pdsmart/tranZPUter/CPLD/SW/tranZPUterSW.vhd

--------------------------------------------------------------------------------------------------------
--
-- Name:            tranZPUterSW.vhd
-- Created:         June 2020
-- Author(s):       Philip Smart
-- Description:     tranZPUter SW v2.1 - v2.2 CPLD logic definition file.
--                  This module contains the definition of the logic used in v1.0-v1.1 of the tranZPUterSW
--                  project plus enhancements.
--
-- Credits:         
-- Copyright:       (c) 2018-20 Philip Smart <philip.smart@net2net.org>
--
-- History:         June 2020 - Initial creation.
--                  July 2020 - Updated and fixed logic, removed the MZ80B compatibility logic as there
--                              are not enough resources in the CPLD to fully implement.
--                  July 2020 - Changed the keyboard mapping logic to be more compatible. A full swepp 
--                              is made if a read is made to the keyboard data twice in a row as this
--                              signifies a game or program reading BREAK. When the software scans the
--                              keyboard the data is stored into a matrix which is then used for mapping
--                              of the keys.  When the running software accesses the keyboard it reads
--                              from the key matrix and not the PPI. This allows for better compatibility
--                              and a functioning SHIFT+BREAK key. The MZ80A keyboard layout is mapped
--                              as though the keyboard was a real MZ700 keyboard, ie. BREAK key is CLR/HOME
--                              and INST/DEL is CTRL etc. The numeric keypad on the MZ80A is mapped to the
--                              cursor key layout with 7 and 9 acting as INST/DEL. The function keys are
--                              mapped to 1, 0, 00, . and 3 on the numeric keypad.
--                  July 2020 - Making RFS updates I decided that a basic board (ie. no K64F) which would
--                              be used in conjunction with the RFS board needs a secondary clock, 
--                              more especially for the MZ700 3.58MHz mode. I thus added a 50MHz clock 
--                              onto the output that would normally be driven by a K64F. This output
--                              is then divided down to act as the secondary clock. When a mode switch
--                              is made to MZ700 mode the frequency automatically changes.
--                  Mar 2021 -  Better control of the external Asyn BUSRQ/BUSACK was needed, bringing in 
--                              Synchronize with the SW700 development.
--                              the async K64F CTL_BUSRQ into the Z80 clocked domain and adjustment of
--                              mux lines.
--                  Mar 2021 -  Many changes to cater for the MZ-800. The machine has different memory
--                              modes and maps so extensive changes needed.
--                  Apr 2021 -  Removed the v2.1 frequency generator as 2.1 no longer supported. Fixed
--                              issues with adding the MZ-800 using too many resources, made 
--                              compilation conditional.
--
---------------------------------------------------------------------------------------------------------
-- This source file is free software: you can redistribute it and-or modify
-- it under the terms of the GNU General Public License as published
-- by the Free Software Foundation, either version 3 of the License, or
-- (at your option) any later version.
--
-- This source file is distributed in the hope that it will be useful,
-- but WITHOUT ANY WARRANTY; without even the implied warranty of
-- MERCHANTABILITY or FITNESS FOR A PARTICULAR PURPOSE.  See the
-- GNU General Public License for more details.
--
-- You should have received a copy of the GNU General Public License
-- along with this program.  If not, see <http:--www.gnu.org-licenses->.
---------------------------------------------------------------------------------------------------------
library ieee;
library pkgs;
use ieee.std_logic_1164.all;
use ieee.std_logic_unsigned.all;
use ieee.numeric_std.all;
use work.tranZPUterSW_pkg.all;

entity cpld512 is
    --generic (
    --);
    port (    
        -- Z80 Address and Data.
        Z80_HI_ADDR               : inout std_logic_vector(23 downto 16);                -- Hi address. These are the upper bank bits allowing 512K of address space. They are directly set by the K64F when accessing RAM or FPGA and set by the FPGA according to memory mode.
        Z80_RA_ADDR               : out   std_logic_vector(15 downto 12);                -- Row address - RAM is subdivided into 4K blocks which can be remapped as needed. This is required for the MZ80B emulation where memory changes location according to mode.
        Z80_ADDR                  : inout std_logic_vector(15 downto 0);
        Z80_DATA                  : inout std_logic_vector( 7 downto 0);

        -- Z80 Control signals.
        Z80_BUSRQn                : out   std_logic;
        Z80_BUSACKn               : in    std_logic;
        Z80_INTn                  : inout std_logic;
        Z80_IORQn                 : in    std_logic;
        Z80_MREQn                 : inout std_logic;
        Z80_NMIn                  : inout std_logic;
        Z80_RDn                   : in    std_logic;
        Z80_WRn                   : in    std_logic;
        Z80_RESETn                : in    std_logic;                                     -- NB. The CPLD inverts the GCLRn pin, so active negative on the mainboard, active positive inside the CPLD.
        Z80_HALTn                 : in    std_logic;
        Z80_WAITn                 : out   std_logic;
        Z80_M1n                   : in    std_logic;
        Z80_RFSHn                 : in    std_logic;
        Z80_CLK                   : out   std_logic;

        -- K64F control signals.
        CTL_MBSEL                 : in    std_logic;                                     -- Select mainboard, 1 = mainboard, 0 = tranzputer bus.
        CTL_BUSRQn                : in    std_logic;
        CTL_BUSACKn               : out   std_logic;                                     -- Combined BUSACK signal to the K64F
        CTL_HALTn                 : out   std_logic;
        CTL_M1n                   : out   std_logic;
        CTL_RFSHn                 : out   std_logic;
        CTL_WAITn                 : in    std_logic;
        SVCREQn                   : out   std_logic;

        -- Mainboard signals which are blended with K64F signals to activate corresponding Z80 functionality.
        SYS_BUSACKn               : out   std_logic;
        SYS_BUSRQn                : in    std_logic;
        SYS_WAITn                 : in    std_logic;
        SYS_WRn                   : out   std_logic;
        SYS_RDn                   : out   std_logic;    

        -- RAM control.
        RAM_CSn                   : out   std_logic;
        RAM_OEn                   : out   std_logic;
        RAM_WEn                   : out   std_logic;

        -- Graphics Board I/O and Memory Select.
        INCLK                     : in    std_logic;
        OUTDATA                   : out   std_logic_vector(3 downto 0);

        -- Clocks, system and K64F generated.
        SYSCLK                    : in    std_logic;                                     -- Mainboard system clock.
        CTLCLK                    : in    std_logic                                      -- K64F generated secondary CPU clock.
    );
end entity;

architecture rtl of cpld512 is

    -- Definition of a keyboard mapping matrix as an array of registers. The host keyboard is
    -- read into the matrix and the output is mapped according to the target.
    --
    type KeyMatrixType is array(natural range 0 to 9) of std_logic_vector(7 downto 0);

    -- Keyboard mapping signals
    signal KEY_MATRIX             :       KeyMatrixType;
    signal KEY_DATA               :       std_logic_vector(7 downto 0);
    signal KEY_STROBE             :       std_logic_vector(3 downto 0);
    signal KEY_STROBE_LAST        :       std_logic_vector(3 downto 0);
    signal KEY_SUBSTITUTE         :       std_logic;
    signal KEY_SWEEP              :       std_logic;
    signal MB_KEY_STROBE          :       std_logic_vector(3 downto 0);
    signal MB_WRITE_STROBE        :       std_logic;
    signal MB_READ_KEYS           :       std_logic;

    -- CPLD configuration signals.
    signal MODE_CPLD_MZ80K        :       std_logic;
    signal MODE_CPLD_MZ80C        :       std_logic;
    signal MODE_CPLD_MZ1200       :       std_logic;
    signal MODE_CPLD_MZ80A        :       std_logic;
    signal MODE_CPLD_MZ700        :       std_logic;
    signal MODE_CPLD_MZ800        :       std_logic;
    signal MODE_CPLD_MZ80B        :       std_logic;
    signal MODE_CPLD_MZ2000       :       std_logic;
    signal MODE_CPLD_SWITCH       :       std_logic;
    signal MODE_CPLD_MB_VIDEOn    :       std_logic;                                     -- Mainboard video, 0 = enabled, 1 = disabled. 
    signal MODE_HOST_DEFAULT      :       std_logic;                                     -- On cold start, the host acts per original specifications until changed by programming.
    signal CPU_CFG_DATA           :       std_logic_vector(7 downto 0):=(others => '0'); -- CPU Configuration register.
    signal CPLD_CFG_DATA          :       std_logic_vector(7 downto 0):=(others => '0'); -- CPLD Configuration register.
    signal CPLD_INFO_DATA         :       std_logic_vector(7 downto 0);                  -- CPLD status value.
    signal VIDEOMODULE_PRESENT    :       std_logic;                                     -- Automatic flag which is set if the serializer becomes active.

    -- IO Decode signals.
    signal CS_IO_6XXn             :       std_logic;                                     -- IO decode for the 0x60-0x6f region used by the CPLD.
    signal CS_MEM_CFGn            :       std_logic;                                     -- Select for the memory mode latch.
    signal CS_SCK_CTLCLKn         :       std_logic;                                     -- Select for setting the K64F clock as the active Z80 clock.
    signal CS_SCK_SYSCLKn         :       std_logic;                                     -- Select for setting the Mainboard clock as the active Z80 clock.
    signal CS_SCK_RDn             :       std_logic;                                     -- Select to read which clock is active.
    signal CS_CPU_CFGn            :       std_logic;                                     -- Select to set the CPU configuration register.
    signal CS_CPU_INFOn           :       std_logic;                                     -- Select to read the CPU information register.
    signal CS_CPLD_CFGn           :       std_logic;                                     -- Select to set the CPLD configuration register.
    signal CS_CPLD_INFOn          :       std_logic;                                     -- Select to read the CPLD information register.
    signal CS_VIDEOn              :       std_logic;                                     -- Primary select of the FPGA video logic, used to enable control signals in the memory management process.
    signal CS_VIDEO_MEMn          :       std_logic;                                     -- Select to read/write video memory according to mode.
    signal CS_VIDEO_IOn           :       std_logic;                                     -- Select to read/write video IO registers according to mode.
    signal CS_VIDEO_RDn           :       std_logic;                                     -- Select to read video memory and video IO registers according to mode.
    signal CS_VIDEO_WRn           :       std_logic;                                     -- Select to write video memory and video IO registers according to mode.
    signal MEM_MODE_LATCH         :       std_logic_vector(4 downto 0):=(others => '0'); -- Register to store the active memory mode.
    signal MEM_MODE_DATA          :       std_logic_vector(7 downto 0);                  -- Scratch signal to form an 8 bit read of the memory mode register.

    -- SR (LS279) state symbols.
    signal SYSCLK_Q               :       std_logic;
    signal CTLCLK_Q               :       std_logic;
    --
    signal DISABLE_BUSn           :       std_logic;                                     -- Signal to disable access to the mainboard (= 0) via the SYS_BUSACKn signal which tri-states the mainboard logic.
    signal SYS_BUSACKni           :       std_logic := '0';                              -- Signal to hold the current state of the SYS_BUSACKn signal used to activate/tri-state the mainboard logic.

    -- CPU Frequency select logic based on Flip Flops and gates.
    signal SCK_CTLSELn            :       std_logic;
    signal Z80_CLKi               :       std_logic;
    signal CTLCLKi                :       std_logic;
    signal CLK_STATUS_DATA        :       std_logic_vector(7 downto 0);

    -- Video module signals.
    --
    signal VZ80_IORQn             :       std_logic;
    signal OUTBUF                 :       std_logic_vector(3 downto 0);

    -- Video module signal mirrors.
    signal MODE_VIDEO_MZ80A       :       std_logic := '1';                              -- The machine is running in MZ80A mode.
    signal MODE_VIDEO_MZ700       :       std_logic := '0';                              -- The machine is running in MZ700 mode.
    signal MODE_VIDEO_MZ800       :       std_logic := '0';                              -- The machine is running in MZ800 mode.
    signal MODE_VIDEO_MZ80B       :       std_logic := '0';                              -- The machine is running in MZ80B mode.
    signal MODE_VIDEO_MZ80K       :       std_logic := '0';                              -- The machine is running in MZ80K mode.
    signal MODE_VIDEO_MZ80C       :       std_logic := '0';                              -- The machine is running in MZ80C mode.
    signal MODE_VIDEO_MZ1200      :       std_logic := '0';                              -- The machine is running in MZ1200 mode.
    signal MODE_VIDEO_MZ2000      :       std_logic := '0';                              -- The machine is running in MZ2000 mode.
    signal GRAM_PAGE_ENABLE       :       std_logic;                                     -- Graphics mode page enable.
    signal MZ80B_VRAM_HI_ADDR     :       std_logic;                                     -- Video RAM located at D000:FFFF when high.
    signal MZ80B_VRAM_LO_ADDR     :       std_logic;                                     -- Video RAM located at 5000:7FFF when high.
    signal CS_FB_VMn              :       std_logic;                                     -- Chip Select for the Video Mode register.
    signal CS_FB_PAGEn            :       std_logic;                                     -- Chip Select for the Page select register.
    signal CS_IO_CXXn             :       std_logic;                                     -- Chip select for block C0:CF
    signal CS_IO_DXXn             :       std_logic;                                     -- Chip select for block D0:DF
    signal CS_IO_EXXn             :       std_logic;                                     -- Chip select for block E0:EF
    signal CS_IO_FXXn             :       std_logic;                                     -- Chip select for block F0:FF
    signal CS_80B_PIOn            :       std_logic;                                     -- Chip select for MZ80B PIO when in MZ80B mode.

    -- Z80 Wait Insert generator when I/O ports in region > 0XE0 are accessed to give the K64F time to proces them.
  --signal REQ_WAITn            :       std_logic;

    -- Internal control signals.
    signal SYSRESETn              :       std_logic;                                     -- Internal system reset pulse 1 clock period after reset, used to preset registers.
    signal Z80_HI_ADDRi           :       std_logic_vector(23 downto 16);                -- Hi address. These are the upper bank bits allowing 512K of address space. They are directly set by the K64F when accessing RAM or FPGA and set by the FPGA according to memory mode.
    signal Z80_RA_ADDRi           :       std_logic_vector(15 downto 12);                -- Row address - RAM is subdivided into 4K blocks which can be remapped as needed. This is required for the MZ80B emulation where memory changes location according to mode.
    signal CTL_BUSACKni           :       std_logic;                                     -- Buffered BUSACK signal to the K64F to indicate it has control of the bus.
    signal CTL_BUSRQni            :       std_logic;                                     -- Buffered BUSRQ signal. 

    -- RAM select and write signals.
    signal RAM_OEni               :       std_logic;
    signal RAM_CSni               :       std_logic;
    signal RAM_WEni               :       std_logic;

    -- MZ800 Memory map signals.
    signal MAP_0000_0FFF_ROM      :       std_logic;                                     --  
    signal MAP_E000_EFFF_ROM      :       std_logic;                                     --  
    signal MAP_F000_FFFF_ROM      :       std_logic;                                     --  
    signal MAP_1000_1FFF_CGROM    :       std_logic;                                     --  

    signal MAP_0000_0FFF_DRAM     :       std_logic;                                     --  
    signal MAP_1000_1FFF_DRAM     :       std_logic;                                     --  
    signal MAP_2000_2FFF_DRAM     :       std_logic;                                     --  
    signal MAP_3000_3FFF_DRAM     :       std_logic;                                     --  
    signal MAP_4000_4FFF_DRAM     :       std_logic;                                     --  
    signal MAP_5000_5FFF_DRAM     :       std_logic;                                     --  
    signal MAP_6000_6FFF_DRAM     :       std_logic;                                     --  
    signal MAP_7000_7FFF_DRAM     :       std_logic;                                     --  
    signal MAP_8000_8FFF_DRAM     :       std_logic;                                     --  
    signal MAP_9000_9FFF_DRAM     :       std_logic;                                     --  
    signal MAP_A000_AFFF_DRAM     :       std_logic;                                     --  
    signal MAP_B000_BFFF_DRAM     :       std_logic;                                     --  
    signal MAP_C000_CFFF_DRAM     :       std_logic;                                     --  
    signal MAP_D000_DFFF_DRAM     :       std_logic;                                     --  
    signal MAP_E000_EFFF_DRAM     :       std_logic;                                     --  
    signal MAP_F000_FFFF_DRAM     :       std_logic;                                     --  
    signal MAP_8000_8FFF_VRAM     :       std_logic;                                     --  
    signal MAP_9000_9FFF_VRAM     :       std_logic;                                     --  
    signal MAP_A000_AFFF_VRAM     :       std_logic;                                     --  
    signal MAP_B000_BFFF_VRAM     :       std_logic;                                     --  
    signal MAP_C000_CFFF_VRAM     :       std_logic;                                     --  
    signal MAP_D000_DFFF_VRAM     :       std_logic;                                     --  
    signal MAP_E000_E00F_IO       :       std_logic;                                     --  
    signal MAP_INHIBIT            :       std_logic;                                     --  
    signal MAP_TZFS_BANK          :       std_logic;                                     -- Override to use Bank 0 in the 512K Static RAM chup rather than the normal Bank 7. This is so TZFS and MZ-800 IPL are seperate and independent allowing change from one to the other.
    signal MODE_320x200           :       std_logic;                                     -- MZ-800 Set to 320x200 graphics mode.
    signal MODE_640x200           :       std_logic;                                     -- MZ-800 Set to 640x200 graphics mode.

    -- MZ800 IO Signals
    signal CS_GDG_GWF             :       std_logic;                                     -- GDG Write Format Register 
    signal CS_GDG_GRF             :       std_logic;                                     -- GDG Read Format Register 
    signal CS_GDG_CMD             :       std_logic;                                     -- GDG Command Register

    -- Mainboard writeback multiplexing signals.
    signal MB_MREQn               :       std_logic;
    signal MB_BUSRQn              :       std_logic;
    signal MB_ADDR                :       std_logic_vector(15 downto 0);
    signal MB_STATE               :       integer range 0 to 7;
    signal MB_WAITn               :       std_logic;
    signal MB_DELAY_MS            :       unsigned(7 downto 0);

    -- Millisecond timer signals.
    signal DELAY_TICKS            :       unsigned(3 downto 0);
    signal DELAY_US               :       unsigned(9 downto 0);
    signal DELAY_MS_CLK           :       std_logic;

    function to_std_logic(L: boolean) return std_logic is
    begin
        if L then
            return('1');
        else
            return('0');
        end if;
    end function to_std_logic;
begin

    -- Delayed reset process to set defaults on registers as required.
    RESET: process( Z80_CLKi, Z80_RESETn ) begin
        if Z80_RESETn = '0' then
            SYSRESETn          <= '0';
        -- First rising edge the internal system reset is cancelled.
        elsif( rising_edge(Z80_CLKi) ) then
            SYSRESETn          <= '1';
        end if;
    end process;

    -- CPLD/CPU Configuration register.
    --
    -- CPU: (NOT YET IMPLEMENTED IN THE traznZPUter)
    -- Version 1.3-> of the tranZPUter SW-700 provides the ability to instantiate alternative soft CPU's. This register configures the FPGA to enable a soft/hard CPU and the CPLD
    -- is reconfigured to allow a CPU operation on the FPGA side rather than the physical hardware side.
    --
    -- [5:0] - R/W - CPU selection.
    --               000000 = Hard CPU
    --               000001 = T80 CPU
    --               000010 = ZPU Evolution
    --               000100 = Future CPU AAA
    --               001000 = Future CPU AAA
    --               010000 = Future CPU AAA
    --               100000 = Future CPU AAA
    --               All other configurations reserved and default to Hard CPU.
    -- [7]   - R/W - CPU Reset. When active ('1'), hold the CPU in reset, when inactive, commence the reset completion and CPU run.
    --
    -- CPLD:
    -- The mode can be changed by a Z80 transaction write into the register and it is acted upon if the mode switches between differing values. The Z80 write is typically used
    -- by host software such as RFS.
    --
    -- [2:0] - R/W - Mode/emulated machine.
    --               000 = MZ-80K
    --               001 = MZ-80C
    --               010 = MZ-1200
    --               011 = MZ-80A
    --               100 = MZ-700
    --               101 = MZ-800
    --               110 = MZ-80B
    --               111 = MZ-2000
    -- [3]   - R/W - Mainboard Video - 0 = Enable, 1 = Disable - This flag allows Z-80 transactions in the range D000:DFFF to be directed to the mainboard. When disabled all transactions
    --                                 can only be seen by the FPGA video logic. The FPGA uses this flag to enable/disable it's functionality.
    --*[4]   - R/W - Enable WAIT state during frame display period. 1 = Enable, 0 = Disable (default). The flag enables Z80 WAIT assertion during the frame display period. Most video modes
    --                                 use double buffering so this isnt needed, but use of direct writes to the frame buffer in 8 colour mode (ie. 640x200 or 320x200 8 colour) there
    --                                 is not enough memory to double buffer so potentially there could be tear or snow, hence this optional wait generator.
    -- [6:5] - R/W - Mainboard/CPU clock.
    --               000 = Sharp MZ80A 2MHz System Clock.
    --               001 = Sharp MZ80B 4MHz System Clock.
    --               010 = Sharp MZ700 3.54MHz System Clock.
    --               011 -111 = Reserved, defaults to 2MHz System Clock.
    --*[7]   - R/W - Preserve configuration over reset (=1) or set to default on reset (=0).
    -- * = SW700 v1.3 only, not used in other CPLD versions.
    --
    MACHINEMODE: process( Z80_CLKi, Z80_RESETn, SYSRESETn, CS_CPU_CFGn, CS_CPLD_CFGn, CPLD_CFG_DATA, CS_CPLD_INFOn, Z80_DATA )
    begin

        if(Z80_RESETn = '0') then
            MODE_CPLD_SWITCH                  <= '0';
            CPU_CFG_DATA(5 downto 0)          <= (others => '0');
            MAP_TZFS_BANK                     <= '0';
            MODE_640x200                      <= '1';
            MODE_320x200                      <= '0';
         --   MODE_HOST_DEFAULT                 <= '0';
--            if CPLD_CFG_DATA(7) = '0' then
--                -- On MZ-800 hardware, reset the mode to MZ800 as it may be in MZ700 mode prior to reset.
--                if CPLD_HOST_HW = MODE_MZ800 then
--                    CPLD_CFG_DATA             <= "10001101";                            -- Enable Sharp MZ-800 host setting, mainboard video unused, wait state unused.
--                else
--                    -- Default to MZ-80A
--                    CPLD_CFG_DATA             <= "10000011";                            -- Default to Sharp MZ80A
--                end if;
--                MODE_HOST_DEFAULT             <= '1';                                   -- Host runs as original until features enabled.
--            end if;

        elsif SYSRESETn = '0' and CPLD_CFG_DATA(7) = '0' then
            -- On MZ-800 hardware, reset the mode to MZ800 as it may be in MZ700 mode prior to reset.
            if CPLD_HOST_HW = MODE_MZ800 then
                CPLD_CFG_DATA             <= "10001101";                            -- Enable Sharp MZ-800 host setting, mainboard video unused, wait state unused.
            else
                -- Default to MZ-80A
                CPLD_CFG_DATA             <= "10000011";                            -- Default to Sharp MZ80A
            end if;
            MODE_HOST_DEFAULT             <= '1';                                   -- Host runs as original until features enabled.

        elsif(rising_edge(Z80_CLKi)) then

            -- Write to CPU config register.
            if(CS_CPU_CFGn = '0' and Z80_WRn = '0') then

                -- Currently this option is not implemented on the tranZPUter SW so set to default Z80 configuration.
                CPU_CFG_DATA(5 downto 0) <= (others => '0');
            
            -- Write to CPLD config register.
            elsif(CS_CPLD_CFGn = '0' and Z80_WRn = '0') then

                -- Set the mode switch event flag if the mode changes.
                if CPLD_CFG_DATA(2 downto 0) /= Z80_DATA(2 downto 0) then
                    MODE_CPLD_SWITCH          <= '1';
                end if;

                -- On the first mode set, if the mode matches the underlying hardware setup a flag so that all the features are enabled.
                -- This mechanism is to allow a machine to behave as original after a cold power-up if the K64F processor is not running or disabled.
                --
                if CPLD_CFG_DATA(2 downto 0) = std_logic_vector(to_unsigned(CPLD_HOST_HW, 3)) then
                    MODE_HOST_DEFAULT         <= '0';
                end if;

                -- Store the new value into the register, used for read operations.
                CPLD_CFG_DATA                 <= Z80_DATA;
            else
                MODE_CPLD_SWITCH              <= '0';
            end if;

            -- On the MZ800 host capture and action the gate array command as it changes the mode.
            if CPLD_HOST_HW = MODE_MZ800 and CS_GDG_CMD = '0' and Z80_WRn = '0' then

                -- Mode 700 command?
                if Z80_DATA(3 downto 0) = "1000" then
                    CPLD_CFG_DATA(2 downto 0) <= std_logic_vector(to_unsigned(MODE_MZ700, 3));

                -- All zeros then switch mode.
                elsif Z80_DATA(3 downto 0) = "0000" then
                    CPLD_CFG_DATA(2 downto 0) <= std_logic_vector(to_unsigned(MODE_MZ800, 3));

                -- Set 320x200 mode?
                elsif Z80_DATA(3 downto 2) = "00" then
                    MODE_640x200              <= '0';
                    MODE_320x200              <= '1';

                -- Set 640x200 mode?
                elsif Z80_DATA(3 downto 2) = "01" then
                    MODE_640x200              <= '1';
                    MODE_320x200              <= '0';
                end if;

                -- A non-standard GDG Command, if bit 7 is set swap ROM banks to allow TZFS to run.
                if Z80_DATA(7) = '1' then
                    MAP_TZFS_BANK             <= '1';
                end if;
            end if;
        end if;
    end process;

    -- MZ-80A/MZ-700 target hardware, generate the original memory management mode logic.
    --
    MEMORYMODE80A: if CPLD_HOST_HW = MODE_MZ80A or CPLD_HOST_HW = MODE_MZ700 generate

        MEMORYMODE: process( Z80_CLKi, Z80_RESETn, SYSRESETn, CS_MEM_CFGn, Z80_IORQn, Z80_WRn, Z80_ADDR, Z80_DATA, CPLD_CFG_DATA, MODE_640x200 )
            variable mz700_LOWER_RAM      : std_logic;
            variable mz700_UPPER_RAM      : std_logic;
            variable mz700_INHIBIT        : std_logic;
            variable MODE_CPLD_LAST       : std_logic_vector(2 downto 0);
        begin

            if(Z80_RESETn = '0') then
                mz700_LOWER_RAM           := '0';
                mz700_UPPER_RAM           := '0';
                mz700_INHIBIT             := '0';
                MODE_CPLD_LAST            := std_logic_vector(to_unsigned(CPLD_HOST_HW, MODE_CPLD_LAST'length));

            -- On power up reset, default to original configuration.
            elsif SYSRESETn = '0' and CPLD_CFG_DATA(7) = '0' then
                -- Default to MZ-700/MZ-80A
                MEM_MODE_LATCH            <= std_logic_vector(to_unsigned(TZMM_ORIG, MEM_MODE_LATCH'length));

            -- A direct write to the memory latch stores the required memory mode into the latch.
            elsif (CS_MEM_CFGn = '0' and Z80_WRn = '0') then
                MEM_MODE_LATCH            <= Z80_DATA(4 downto 0);

            elsif(Z80_CLKi'event and Z80_CLKi = '1') then

                -- Each clock remember the current mode to detect a change.
                MODE_CPLD_LAST            := CPLD_CFG_DATA(2 downto 0);

                -- Check for MZ700 Mode memory changes and adjust current memory mode setting.
                --
                if(MODE_CPLD_MZ700 = '1' and Z80_IORQn = '0' and Z80_M1n = '1' and Z80_ADDR(7 downto 3) = "11100") then

                    -- MZ700 memory mode switch?
                    --         0x0000:0x0FFF     0xD000:0xFFFF
                    -- 0xE0 =  DRAM
                    -- 0xE1 =                    DRAM
                    -- 0xE2 =  MONITOR
                    -- 0xE3 =                    Memory Mapped I/O
                    -- 0xE4 =  MONITOR           Memory Mapped I/O
                    -- 0xE5 =                    Inhibit
                    -- 0xE6 =                    Return to state prior to 0xE5
                    case Z80_ADDR(2 downto 0) is
                        -- 0xE0
                        when "000" =>
                            mz700_LOWER_RAM            := '1';

                        -- 0xE1
                        when "001" =>
                            mz700_UPPER_RAM            := '1';

                        -- 0xE2
                        when "010" =>
                            mz700_LOWER_RAM            := '0';

                        -- 0xE3
                        when "011" =>
                            mz700_UPPER_RAM            := '0';

                        -- 0xE4
                        when "100" =>
                            mz700_LOWER_RAM            := '0';
                            mz700_UPPER_RAM            := '0';

                        -- 0xE5
                        when "101" =>
                            mz700_INHIBIT              := '1';

                        -- 0xE6
                        when "110" =>
                            mz700_INHIBIT              := '0';

                        -- 0xE7
                        when "111" =>
                    end case;

                    if(mz700_INHIBIT = '0' and mz700_LOWER_RAM = '0' and mz700_UPPER_RAM = '0') then
                        MEM_MODE_LATCH(4 downto 0)     <= std_logic_vector(to_unsigned(TZMM_TZFS,    MEM_MODE_LATCH'length));

                    elsif(mz700_INHIBIT = '0' and mz700_LOWER_RAM = '1' and mz700_UPPER_RAM = '0') then
                        MEM_MODE_LATCH(4 downto 0)     <= std_logic_vector(to_unsigned(TZMM_MZ700_0, MEM_MODE_LATCH'length));

                    elsif(mz700_INHIBIT = '0' and mz700_LOWER_RAM = '0' and mz700_UPPER_RAM = '1') then
                        MEM_MODE_LATCH(4 downto 0)     <= std_logic_vector(to_unsigned(TZMM_MZ700_1, MEM_MODE_LATCH'length));

                    elsif(mz700_INHIBIT = '0' and mz700_LOWER_RAM = '1' and mz700_UPPER_RAM = '1') then
                        MEM_MODE_LATCH(4 downto 0)     <= std_logic_vector(to_unsigned(TZMM_MZ700_2, MEM_MODE_LATCH'length));

                    elsif(mz700_INHIBIT = '1' and mz700_LOWER_RAM = '0') then
                        MEM_MODE_LATCH(4 downto 0)     <= std_logic_vector(to_unsigned(TZMM_MZ700_3, MEM_MODE_LATCH'length));

                    elsif(mz700_INHIBIT = '1' and mz700_LOWER_RAM = '1') then
                        MEM_MODE_LATCH(4 downto 0)     <= std_logic_vector(to_unsigned(TZMM_MZ700_4, MEM_MODE_LATCH'length));
                    else
                        null;
                    end if;

                -- Unknown event!
                else
                    null;
                end if;
            end if;
        end process;
    end generate;

    -- MZ-800 target hardware, generate the newer memory management mode logic.
    --
    MEMORYMODE800: if CPLD_HOST_HW = MODE_MZ800 generate

        -- Memory mode latch. This latch stores the current memory mode (or Bank Paging Scheme) according to the running software.
        --
        MEMORYMODE: process( Z80_CLKi, Z80_RESETn, SYSRESETn, CS_MEM_CFGn, Z80_IORQn, Z80_WRn, Z80_ADDR, Z80_DATA, CPLD_CFG_DATA, MODE_640x200 )
            variable mz700_LOWER_RAM      : std_logic;
            variable mz700_UPPER_RAM      : std_logic;
            variable mz700_INHIBIT        : std_logic;
            variable MODE_CPLD_LAST       : std_logic_vector(2 downto 0);
        begin

            if(Z80_RESETn = '0') then
    --            -- On power up reset, default to original configuration.
    --            if CPLD_CFG_DATA(7) = '0' then
    --                -- Default to MZ-700/MZ-80A
    --                MEM_MODE_LATCH        <= std_logic_vector(to_unsigned(TZMM_ORIG, MEM_MODE_LATCH'length));
    --
    --            -- MZ-800 mode
    --            --elsif CPLD_HOST_HW = MODE_MZ800 then
    --            --    MEM_MODE_LATCH        <= std_logic_vector(to_unsigned(TZMM_MZ800, MEM_MODE_LATCH'length));
    --            end if;
                mz700_LOWER_RAM           := '0';
                mz700_UPPER_RAM           := '0';
                mz700_INHIBIT             := '0';

                -- Setup MZ-800 control on reset to MZ-800 startup memory map.
                MAP_0000_0FFF_ROM         <= '1';
                MAP_1000_1FFF_CGROM       <= '1';
                MAP_2000_2FFF_DRAM        <= '1';
                MAP_3000_3FFF_DRAM        <= '1';
                MAP_4000_4FFF_DRAM        <= '1';
                MAP_5000_5FFF_DRAM        <= '1';
                MAP_6000_6FFF_DRAM        <= '1';
                MAP_7000_7FFF_DRAM        <= '1';
                MAP_A000_AFFF_DRAM        <= not MODE_640x200;
                MAP_B000_BFFF_DRAM        <= not MODE_640x200;
                MAP_C000_CFFF_DRAM        <= '1';
                MAP_D000_DFFF_DRAM        <= '1';
                MAP_8000_8FFF_VRAM        <= '1';
                MAP_9000_9FFF_VRAM        <= '1';
                MAP_A000_AFFF_VRAM        <= MODE_640x200;
                MAP_B000_BFFF_VRAM        <= MODE_640x200;
                MAP_E000_EFFF_ROM         <= '1';
                MAP_F000_FFFF_ROM         <= '1';
                -- Clear remaining flags.
                MAP_0000_0FFF_DRAM        <= '0';
                MAP_1000_1FFF_DRAM        <= '0';
                MAP_8000_8FFF_DRAM        <= '0';
                MAP_9000_9FFF_DRAM        <= '0';
                MAP_E000_EFFF_DRAM        <= '0';
                MAP_F000_FFFF_DRAM        <= '0';
                MAP_C000_CFFF_VRAM        <= '0';
                MAP_D000_DFFF_VRAM        <= '0';
                MAP_E000_E00F_IO          <= '0';
                MAP_INHIBIT               <= '0';

                MODE_CPLD_LAST            := std_logic_vector(to_unsigned(CPLD_HOST_HW, MODE_CPLD_LAST'length));

            -- On power up reset, default to original configuration.
            elsif SYSRESETn = '0' and CPLD_CFG_DATA(7) = '0' then
                -- Default to MZ-700/MZ-80A
                MEM_MODE_LATCH            <= std_logic_vector(to_unsigned(TZMM_ORIG, MEM_MODE_LATCH'length));

                -- MZ-800 mode
                --elsif CPLD_HOST_HW = MODE_MZ800 then
                --    MEM_MODE_LATCH        <= std_logic_vector(to_unsigned(TZMM_MZ800, MEM_MODE_LATCH'length));
     

            -- A direct write to the memory latch stores the required memory mode into the latch.
            elsif (CS_MEM_CFGn = '0' and Z80_WRn = '0') then
                MEM_MODE_LATCH            <= Z80_DATA(4 downto 0);

            elsif(Z80_CLKi'event and Z80_CLKi = '1') then

                -- Cater for mode switches made by software between the MZ800 and MZ700 modes.
                --.
    --            if MODE_CPLD_LAST = MODE_MZ700 and MODE_CPLD_MZ800 = '1' then
    --                MAP_0000_0FFF_ROM     <= '1';
    --                MAP_1000_1FFF_CGROM   <= '1';
    --                MAP_2000_2FFF_DRAM    <= '1';
    --                MAP_3000_3FFF_DRAM    <= '1';
    --                MAP_4000_4FFF_DRAM    <= '1';
    --                MAP_5000_5FFF_DRAM    <= '1';
    --                MAP_6000_6FFF_DRAM    <= '1';
    --                MAP_7000_7FFF_DRAM    <= '1';
    --                MAP_A000_AFFF_DRAM    <= not MODE_640x200;
    --                MAP_B000_BFFF_DRAM    <= not MODE_640x200;
    --                MAP_C000_CFFF_DRAM    <= '1';
    --                MAP_D000_DFFF_DRAM    <= '1';
    --                MAP_8000_8FFF_VRAM    <= '1';
    --                MAP_9000_9FFF_VRAM    <= '1';
    --                MAP_A000_AFFF_VRAM    <= MODE_640x200;
    --                MAP_B000_BFFF_VRAM    <= MODE_640x200;
    --                MAP_E000_EFFF_ROM     <= '1';
    --                MAP_F000_FFFF_ROM     <= '1';
    --                -- Clear remaining flags.
    --                MAP_0000_0FFF_DRAM    <= '0';
    --                MAP_1000_1FFF_DRAM    <= '0';
    --                MAP_8000_8FFF_DRAM    <= '0';
    --                MAP_9000_9FFF_DRAM    <= '0';
    --                MAP_E000_EFFF_DRAM    <= '0';
    --                MAP_F000_FFFF_DRAM    <= '0';
    --                MAP_C000_CFFF_VRAM    <= '0';
    --                MAP_D000_DFFF_VRAM    <= '0';
    --                MAP_E000_E00F_IO      <= '0';
    --                MAP_INHIBIT           <= '0';
    --
    --            elsif MODE_CPLD_LAST = MODE_MZ800 and MODE_CPLD_MZ700 = '1' then
    --                MAP_0000_0FFF_ROM     <= '1';
    --                MAP_1000_1FFF_DRAM    <= '1';
    --                MAP_2000_2FFF_DRAM    <= '1';
    --                MAP_3000_3FFF_DRAM    <= '1';
    --                MAP_4000_4FFF_DRAM    <= '1';
    --                MAP_5000_5FFF_DRAM    <= '1';
    --                MAP_6000_6FFF_DRAM    <= '1';
    --                MAP_7000_7FFF_DRAM    <= '1';
    --                MAP_8000_8FFF_DRAM    <= '1';
    --                MAP_9000_9FFF_DRAM    <= '1';
    --                MAP_A000_AFFF_DRAM    <= '1';
    --                MAP_B000_BFFF_DRAM    <= '1';
    --                MAP_C000_CFFF_DRAM    <= '1';
    --                MAP_D000_DFFF_VRAM    <= '1';
    --                MAP_E000_E00F_IO      <= '1';
    --                MAP_E000_EFFF_ROM     <= '1';
    --                MAP_F000_FFFF_ROM     <= '1';
    --                -- Clear remaining flags.
    --                MAP_1000_1FFF_CGROM   <= '0';
    --                MAP_0000_0FFF_DRAM    <= '0';
    --                MAP_D000_DFFF_DRAM    <= '0';
    --                MAP_E000_EFFF_DRAM    <= '0';
    --                MAP_F000_FFFF_DRAM    <= '0';
    --                MAP_8000_8FFF_VRAM    <= '0';
    --                MAP_9000_9FFF_VRAM    <= '0';
    --                MAP_A000_AFFF_VRAM    <= '0';
    --                MAP_B000_BFFF_VRAM    <= '0';
    --                MAP_C000_CFFF_VRAM    <= '0';
    --                MAP_INHIBIT           <= '0';
    --
    --            end if;

                -- Each clock remember the current mode to detect a change.
                MODE_CPLD_LAST            := CPLD_CFG_DATA(2 downto 0);

                -- MZ700/MZ800 memory mode switch?
                --
                --             MZ-700                                                     MZ-800
                --            |0000:0FFF|1000:1FFF|1000:CFFF|C000:CFFF|D000:FFFF          |0000:7FFF|1000:1FFF|2000:7FFF|8000:BFFF|C000:CFFF|C000:DFFF|E000:FFFF
                --            --------------------------------------------------          ----------------------------------------------------------------------
                -- OUT 0xE0 = |DRAM     |         |         |         |                   |DRAM     |         |         |         |         |         |            
                -- OUT 0xE1 = |         |         |         |         |DRAM               |         |         |         |         |         |         |DRAM
                -- OUT 0xE2 = |MONITOR  |         |         |         |                   |MONITOR  |         |         |         |         |         |             
                -- OUT 0xE3 = |         |         |         |         |Memory Mapped I/O  |         |         |         |         |         |         |Upper MONITOR ROM             
                -- OUT 0xE4 = |MONITOR  |         |DRAM     |         |Memory Mapped I/O  |MONITOR  |CGROM    |DRAM     |VRAM     |         |DRAM     |Upper MONITOR ROM
                -- OUT 0xE5 = |         |         |         |         |Inhibit            |         |         |         |         |         |         |Inhibit
                -- OUT 0xE6 = |         |         |         |         |<return>           |         |         |         |         |         |         |<return>
                -- IN  0xE0 = |         |CGROM*   |         |VRAM*    |                   |         |CGROM    |         |VRAM     |         |         |              
                -- IN  0xE1 = |         |DRAM     |         |DRAM     |                   |         |<return> |         |DRAM     |         |         |                                                                           
                --
                -- <return> = Return to the state prior to the complimentary command being invoked.
                -- * = MZ-800 host only.

                -- On MZ-800 hardware the MZ-700 mode is not quite the same so I've elected to use seperate decoding. You thus have MZ700/MZ800 modes on MZ800 hardware and MZ700 modes on 
                -- MZ700/MZ-80A hardware.
                --
                if((MODE_CPLD_MZ700 = '1' or MODE_CPLD_MZ800 = '1') and Z80_IORQn = '0' and Z80_M1n = '1' and Z80_ADDR(7 downto 3) = "11100") then

                    case Z80_ADDR(2 downto 0) is
                        -- 0xE0
                        when "000" =>
                            -- To cater for the CGROM being paged into the address space we use an override rather than a seperate memory mode.
                            if Z80_RDn = '0' then
                                MAP_1000_1FFF_DRAM     <= '0';
                                MAP_1000_1FFF_CGROM    <= '1';
                                if MODE_CPLD_MZ800 = '1' then
                                    MAP_8000_8FFF_VRAM <= '1';
                                    MAP_9000_9FFF_VRAM <= '1';
                                    MAP_A000_AFFF_VRAM <= MODE_640x200;
                                    MAP_B000_BFFF_VRAM <= MODE_640x200;
                                    MAP_8000_8FFF_DRAM <= '0';
                                    MAP_9000_9FFF_DRAM <= '0';
                                    MAP_A000_AFFF_DRAM <= not MODE_640x200;
                                    MAP_B000_BFFF_DRAM <= not MODE_640x200;
                                else
                                    MAP_C000_CFFF_VRAM <= '1';
                                    MAP_C000_CFFF_DRAM <= '0';
                                end if;

                            elsif MODE_CPLD_MZ800 = '1' then
                                MAP_0000_0FFF_DRAM     <= '1';
                                MAP_1000_1FFF_DRAM     <= '1';
                                MAP_2000_2FFF_DRAM     <= '1';
                                MAP_3000_3FFF_DRAM     <= '1';
                                MAP_4000_4FFF_DRAM     <= '1';
                                MAP_5000_5FFF_DRAM     <= '1';
                                MAP_6000_6FFF_DRAM     <= '1';
                                MAP_7000_7FFF_DRAM     <= '1';
                                MAP_0000_0FFF_ROM      <= '0';
                                MAP_1000_1FFF_CGROM    <= '0';
                            else
                                MAP_0000_0FFF_DRAM     <= '1';
                                MAP_1000_1FFF_DRAM     <= '1';
                                MAP_2000_2FFF_DRAM     <= '1';
                                MAP_3000_3FFF_DRAM     <= '1';
                                MAP_4000_4FFF_DRAM     <= '1';
                                MAP_5000_5FFF_DRAM     <= '1';
                                MAP_6000_6FFF_DRAM     <= '1';
                                MAP_7000_7FFF_DRAM     <= '1';
                                MAP_8000_8FFF_DRAM     <= '1';
                                MAP_9000_9FFF_DRAM     <= '1';
                                MAP_A000_AFFF_DRAM     <= '1';
                                MAP_B000_BFFF_DRAM     <= '1';
                                MAP_C000_CFFF_DRAM     <= '1';
                                MAP_0000_0FFF_ROM      <= '0';
                                MAP_1000_1FFF_CGROM    <= '0';
                            end if;

                        -- 0xE1
                        when "001" =>
                            if Z80_RDn = '0' then
                                MAP_1000_1FFF_DRAM     <= '1';
                                MAP_1000_1FFF_CGROM    <= '0';

                                if MODE_CPLD_MZ800 = '1' then
                                    MAP_8000_8FFF_DRAM <= '1';
                                    MAP_9000_9FFF_DRAM <= '1';
                                    MAP_A000_AFFF_DRAM <= '1';
                                    MAP_B000_BFFF_DRAM <= '1';
                                    MAP_8000_8FFF_VRAM <= '0';
                                    MAP_9000_9FFF_VRAM <= '0';
                                    MAP_A000_AFFF_VRAM <= '0';
                                    MAP_B000_BFFF_VRAM <= '0';
                                else
                                    MAP_C000_CFFF_DRAM <= '1';
                                    MAP_C000_CFFF_VRAM <= '0';
                                end if;

                            elsif MODE_CPLD_MZ800 = '1' then
                                MAP_E000_EFFF_DRAM     <= '1';
                                MAP_F000_FFFF_DRAM     <= '1';
                                MAP_E000_EFFF_ROM      <= '0';
                                MAP_F000_FFFF_ROM      <= '0';
                                MAP_E000_E00F_IO       <= '0';
                            else
                                MAP_D000_DFFF_DRAM     <= '1';
                                MAP_E000_EFFF_DRAM     <= '1';
                                MAP_F000_FFFF_DRAM     <= '1';
                                MAP_D000_DFFF_VRAM     <= '0';
                                MAP_E000_EFFF_ROM      <= '0';
                                MAP_F000_FFFF_ROM      <= '0';
                                MAP_E000_E00F_IO       <= '0';
                            end if;

                        -- 0xE2
                        when "010" =>
                            MAP_0000_0FFF_ROM          <= '1';
                            MAP_0000_0FFF_DRAM         <= '0';

                        -- 0xE3
                        when "011" =>
                            if MODE_CPLD_MZ800 = '1' then
                                MAP_E000_EFFF_ROM      <= '1';
                                MAP_F000_FFFF_ROM      <= '1';
                                MAP_E000_E00F_IO       <= '0';
                                MAP_E000_EFFF_DRAM     <= '0';
                                MAP_F000_FFFF_DRAM     <= '0';
                            else
                                MAP_D000_DFFF_VRAM     <= '1';
                                MAP_E000_E00F_IO       <= '1';
                                MAP_E000_EFFF_ROM      <= '1';
                                MAP_F000_FFFF_ROM      <= '1';
                            end if;

                        -- 0xE4
                        when "100" =>
                            if MODE_CPLD_MZ800 = '1' then
                                MAP_0000_0FFF_ROM      <= '1';
                                MAP_1000_1FFF_CGROM    <= '1';
                                MAP_2000_2FFF_DRAM     <= '1';
                                MAP_3000_3FFF_DRAM     <= '1';
                                MAP_4000_4FFF_DRAM     <= '1';
                                MAP_5000_5FFF_DRAM     <= '1';
                                MAP_6000_6FFF_DRAM     <= '1';
                                MAP_7000_7FFF_DRAM     <= '1';
                                MAP_A000_AFFF_DRAM     <= not MODE_640x200;
                                MAP_B000_BFFF_DRAM     <= not MODE_640x200;
                                MAP_C000_CFFF_DRAM     <= '1';
                                MAP_D000_DFFF_DRAM     <= '1';
                                MAP_8000_8FFF_VRAM     <= '1';
                                MAP_9000_9FFF_VRAM     <= '1';
                                MAP_A000_AFFF_VRAM     <= MODE_640x200;
                                MAP_B000_BFFF_VRAM     <= MODE_640x200;
                                MAP_E000_EFFF_ROM      <= '1';
                                MAP_F000_FFFF_ROM      <= '1';
                                -- Clear remaining flags.
                                MAP_0000_0FFF_DRAM     <= '0';
                                MAP_1000_1FFF_DRAM     <= '0';
                                MAP_8000_8FFF_DRAM     <= '0';
                                MAP_9000_9FFF_DRAM     <= '0';
                                MAP_E000_EFFF_DRAM     <= '0';
                                MAP_F000_FFFF_DRAM     <= '0';
                                MAP_C000_CFFF_VRAM     <= '0';
                                MAP_D000_DFFF_VRAM     <= '0';
                                MAP_E000_E00F_IO       <= '0';
                                MAP_INHIBIT            <= '0';

                            else
                                MAP_0000_0FFF_ROM      <= '1';
                                MAP_1000_1FFF_DRAM     <= '1';
                                MAP_2000_2FFF_DRAM     <= '1';
                                MAP_3000_3FFF_DRAM     <= '1';
                                MAP_4000_4FFF_DRAM     <= '1';
                                MAP_5000_5FFF_DRAM     <= '1';
                                MAP_6000_6FFF_DRAM     <= '1';
                                MAP_7000_7FFF_DRAM     <= '1';
                                MAP_8000_8FFF_DRAM     <= '1';
                                MAP_9000_9FFF_DRAM     <= '1';
                                MAP_A000_AFFF_DRAM     <= '1';
                                MAP_B000_BFFF_DRAM     <= '1';
                                MAP_C000_CFFF_DRAM     <= '1';
                                MAP_D000_DFFF_VRAM     <= '1';
                                MAP_E000_E00F_IO       <= '1';
                                MAP_E000_EFFF_ROM      <= '1';
                                MAP_F000_FFFF_ROM      <= '1';
                                -- Clear remaining flags.
                                MAP_0000_0FFF_DRAM     <= '0';
                                MAP_1000_1FFF_CGROM    <= '0';
                                MAP_D000_DFFF_DRAM     <= '0';
                                MAP_E000_EFFF_DRAM     <= '0';
                                MAP_F000_FFFF_DRAM     <= '0';
                                MAP_8000_8FFF_VRAM     <= '0';
                                MAP_9000_9FFF_VRAM     <= '0';
                                MAP_A000_AFFF_VRAM     <= '0';
                                MAP_B000_BFFF_VRAM     <= '0';
                                MAP_C000_CFFF_VRAM     <= '0';
                                MAP_INHIBIT            <= '0';
                            end if;

                        -- 0xE5
                        when "101" =>
                            MAP_INHIBIT                <= '1';

                        -- 0xE6
                        when "110" =>
                            MAP_INHIBIT                <= '0';

                        -- 0xE7
                        when "111" =>
                    end case;

                    -- Single memory map mode to handle the MZ-800, decoding is done in the memory management process.
                    if MODE_HOST_DEFAULT = '0' then
                        MEM_MODE_LATCH(4 downto 0)     <= std_logic_vector(to_unsigned(TZMM_MZ800, MEM_MODE_LATCH'length));
                    end if;

                -- Unknown event!
                else
                    null;
                end if;
            end if;
        end process;
    end generate;

    -- Process to map host keyboard to realise compatibility with other Sharp machines.
    -- Currently the host can be a Sharp MZ-80A or MZ-800. Target (emulated) machines will be mapped accordingly.
    -- will appear as the target keyboard.
    USEKEYMAPPER: if CPLD_HOST_HW = MODE_MZ80A generate

        KEYMAPPER: process( Z80_CLKi, Z80_RESETn, CS_MEM_CFGn, Z80_IORQn, Z80_ADDR, Z80_DATA )
            variable DELAY_MS_CLK_LAST  : std_logic;
        begin

            if Z80_RESETn = '0' then
                KEY_SUBSTITUTE          <= '0';
                KEY_SWEEP               <= '0';
                MB_STATE                <= 0;
                MB_BUSRQn               <= '1';
                MB_MREQn                <= '1';
                MB_WRITE_STROBE         <= '0';
                MB_READ_KEYS            <= '0';
                MB_WAITn                <= '1';
                MB_ADDR                 <= (others => '0');
                MB_DELAY_MS             <= (others => '0');
                MB_KEY_STROBE           <= (others => '0');
                KEY_STROBE              <= (others => '0');
                KEY_STROBE_LAST         <= (others => '0');

            elsif Z80_CLKi'event and Z80_CLKi = '1' then

                -- Millisecond down counter.
                if DELAY_MS_CLK = '1' and DELAY_MS_CLK_LAST = '0' then
                    if MB_DELAY_MS /= 0 then
                        MB_DELAY_MS     <= MB_DELAY_MS - 1;
                    end if;
                end if;
                DELAY_MS_CLK_LAST       := DELAY_MS_CLK;

                -- When inactive, wait for a Z80 I/O transaction that needs writeback.
                --
                if MODE_CPLD_MZ700 = '1' then

                    -- Auto scanning state machine. When the MZ700 isnt scanning the keys this FSM scans them to be ready
                    -- to respond to events such as BREAK key detection. Normally the FSM wont run as the MZ700 scans the keys in
                    -- software but when the MZ700 runs some kinds of software the scans stop and occasionally the BREAK/SHIFT line 9 is scanned.
                    -- Under these circumstances the FSM will make a full sweep of the keys.
                    --
                    -- Configurable delay, a tick by tick timer and a millisecond timer, halts all actions whilst the timer > 0.
                    if MB_DELAY_MS /= 0 then

                    -- If the Z80 Bus has not been requested and we need to make a key sweep, request the bus and start the sweep.
                    elsif Z80_MREQn = '1' and MB_BUSRQn = '1' and MB_WAITn = '1' and KEY_SWEEP = '1' and KEY_SUBSTITUTE = '0' then
                        MB_BUSRQn       <= '0';

                    -- When the Z80 bus is available, run the FSM.
                    elsif MB_BUSRQn = '0' and Z80_BUSACKn = '0' then

                        -- Move along the state machine, next state can be overriden if required.
                        --
                        if MB_STATE = 6 then
                            MB_STATE                <= 0;
                        else
                            MB_STATE                <= MB_STATE+1;
                        end if;

                        -- FSM.
                        case MB_STATE is
                            -- Setup to write the strobe value to PPI A.
                            when 0 =>
                                MB_ADDR             <= X"E000";
                                KEY_DATA            <= "1111" & MB_KEY_STROBE;
        
                            -- Allow at least 1 cycles for the MREQ signal to settle.
                            when 1 =>
                                MB_MREQn            <= '0';

                            -- Allow at least 1 cycle for the write pulse.
                            when 2 =>
                                MB_WRITE_STROBE     <= '1';
        
                            -- Terminate write pulse.
                            when 3 =>
                                MB_MREQn            <= '1';
                                MB_WRITE_STROBE     <= '0';
        
                            -- Setup for a read of the key data from PPI B.
                            when 4 =>
                                MB_ADDR             <= X"E001";
        
                            -- Allow at least 2 cycles for the data to become available.
                            when 5 =>
                                MB_MREQn            <= '0';
                                MB_READ_KEYS        <= '1';
        
                            -- Read the key data into the matrix for later mapping.
                            when 6 =>
                                KEY_MATRIX(to_integer(unsigned(MB_KEY_STROBE))) <= Z80_DATA;
                                MB_MREQn            <= '1';
                                MB_READ_KEYS        <= '0';
        
                                if unsigned(MB_KEY_STROBE) = 9 then
                                    MB_KEY_STROBE   <= (others => '0');
                                    MB_DELAY_MS     <= X"FA";                     -- 250ms delay between key sweeps with a 3.58MHz clock to prevent excessive scanning.
                                    KEY_SWEEP       <= '0';
                                    MB_BUSRQn       <= '1';
                                else
                                    MB_KEY_STROBE   <= MB_KEY_STROBE + 1;
                                    MB_BUSRQn       <= '1';
                                end if;
        
                            when others =>
                                MB_STATE            <= 0;
                        end case;
                    end if;

                    -- When the Z80 isnt tri-stated process the memory operations and act on required triggers.
                    --
                    if MB_BUSRQn = '1' and Z80_BUSACKn = '1' then
                        -- Detect a strobe output write and store it - this is used as the index into the key matrix for each read operation.
                        if(Z80_MREQn = '0' and Z80_ADDR(15 downto 0) = X"E000" and Z80_DATA(7) = '1') then
                            KEY_STROBE              <= Z80_DATA(3 downto 0);
                        end if;

                        -- On a keyscan read data into the matrix and raise the substitue flag. This flag will disable the mainboard (tri-state it) so that the data lines are not driven. The mapped
                        -- data is then output on the data bus by the CPLD which the Z80 reads.
                        if(Z80_MREQn = '0' and Z80_ADDR(15 downto 0) = X"E001") then

                            -- If this is the first loop, set a 1 cycle wait to allow us to read in the scanned data before overriding with the mapped data. The Z80 cycle is short so without the wait
                            -- we cant reliably read the data being output from the 8255.
                            if MB_WAITn = '1' and KEY_SUBSTITUTE = '0' then
                                MB_WAITn            <= '0';
                                MB_BUSRQn           <= '1'; 
                            else
                                -- 2nd cycle we release the WAIT state and override the data being output by the 8255 with the mapped equivalent.
                                MB_WAITn            <= '1';
                                KEY_SUBSTITUTE      <= '1';

                                -- On the 2nd loop the data from the 8255 key scan has settled on the bus so can be captured.
                                if KEY_SUBSTITUTE = '0' then
                                    KEY_MATRIX(to_integer(unsigned(KEY_STROBE))) <= Z80_DATA;
                                end if;

                                -- Remember last key strobe as we need to detect a scan to the same row more than once, this is typically used for BREAK detection or single key detection.
                                -- In these cases we make an automated sweep of the entire keyboard as keys on the host are spread out on different strobe lines whereas the machine we are mapping to
                                -- has them on one strobe line.
                                KEY_STROBE_LAST     <= KEY_STROBE;
                                if KEY_STROBE_LAST = KEY_STROBE and KEY_SWEEP = '0' then
                                    KEY_SWEEP       <= '1';
                                end if;
                            end if;

                            -- Actual keyboard mapping. The Sharp MZ-80A key codes are scanned into a 10x8 matrix and then this matrix is indexed to extract the keycodes for the machine we
                            -- are being compatible with.
                            --
                            -- MZ-80A Keyboard -> MZ-700 mapping.
                            if MODE_CPLD_MZ700 = '1' then
                                case KEY_STROBE is
                                    --                     D7                D6                D5                D4                D3                D2                D1                D0
                                    when "0000" =>
                                        KEY_DATA        <= '1'              & KEY_MATRIX(0)(7) & KEY_MATRIX(7)(4) & KEY_MATRIX(0)(1) & '1'              & KEY_MATRIX(6)(2) & KEY_MATRIX(6)(3) & KEY_MATRIX(7)(3);  -- 1
                                    when "0001" =>
                                        KEY_DATA        <= KEY_MATRIX(3)(5) & KEY_MATRIX(1)(0) & KEY_MATRIX(6)(4) & KEY_MATRIX(6)(5) & KEY_MATRIX(7)(2) & '1'              & '1'              & '1'             ;  -- 2
                                    when "0010" =>
                                        KEY_DATA        <= KEY_MATRIX(1)(4) & KEY_MATRIX(2)(5) & KEY_MATRIX(2)(2) & KEY_MATRIX(3)(4) & KEY_MATRIX(4)(4) & KEY_MATRIX(3)(1) & KEY_MATRIX(1)(5) & KEY_MATRIX(2)(1);  -- 3
                                    when "0011" =>
                                        KEY_DATA        <= KEY_MATRIX(4)(5) & KEY_MATRIX(4)(3) & KEY_MATRIX(5)(2) & KEY_MATRIX(5)(3) & KEY_MATRIX(5)(0) & KEY_MATRIX(4)(1) & KEY_MATRIX(5)(4) & KEY_MATRIX(5)(5);  -- 4
                                    when "0100" =>
                                        KEY_DATA        <= KEY_MATRIX(1)(3) & KEY_MATRIX(3)(0) & KEY_MATRIX(2)(0) & KEY_MATRIX(2)(3) & KEY_MATRIX(2)(4) & KEY_MATRIX(3)(2) & KEY_MATRIX(3)(3) & KEY_MATRIX(4)(2);  -- 5
                                    when "0101" =>
                                        KEY_DATA        <= KEY_MATRIX(1)(6) & KEY_MATRIX(1)(7) & KEY_MATRIX(2)(6) & KEY_MATRIX(2)(7) & KEY_MATRIX(3)(6) & KEY_MATRIX(3)(7) & KEY_MATRIX(4)(6) & KEY_MATRIX(4)(7);  -- 6
                                    when "0110" =>
                                        KEY_DATA        <= KEY_MATRIX(7)(6) & KEY_MATRIX(6)(7) & KEY_MATRIX(6)(6) & KEY_MATRIX(4)(0) & KEY_MATRIX(5)(7) & KEY_MATRIX(5)(6) & KEY_MATRIX(5)(1) & KEY_MATRIX(6)(0);  -- 7
                                    when "0111" =>
                                        KEY_DATA        <= KEY_MATRIX(8)(6) & KEY_MATRIX(9)(6) & KEY_MATRIX(8)(7) & KEY_MATRIX(8)(3) & KEY_MATRIX(9)(4) & KEY_MATRIX(8)(4) & KEY_MATRIX(7)(0) & KEY_MATRIX(6)(1);  -- 8
                                    when "1000" =>
                                        KEY_DATA        <= KEY_MATRIX(7)(7) & KEY_MATRIX(1)(2) & '1'              & '1'              & '1'              & '1'             & '1'               & KEY_MATRIX(0)(0);  -- 9
                                    when "1001" =>
                                        KEY_DATA        <= KEY_MATRIX(8)(2) & KEY_MATRIX(8)(0) & KEY_MATRIX(8)(1) & KEY_MATRIX(9)(0) & KEY_MATRIX(9)(2) & '1'             & '1'               & '1'             ;  -- 10
                                    when others =>
                                        KEY_DATA        <= "11111111";
                                end case;
                            end if;
                        end if;

                        -- When the Z80_MREQn goes inactive, the keyboard read has completed so clear the substitute flag which in turn allows normal bus operations.
                        --
                        if(KEY_SUBSTITUTE = '1' and Z80_MREQn = '1') then
                            KEY_SUBSTITUTE          <= '0';
                        end if;
                    end if;
                else
                    -- Standard mode we dont use the MB logic so set to default.
                    MB_BUSRQn           <= '1';
                    MB_STATE            <= 0;
                end if;
            end if;
        end process;
    else generate
        KEY_SUBSTITUTE          <= '0';
        MB_BUSRQn               <= '1';
        MB_MREQn                <= '1';
        MB_WRITE_STROBE         <= '0';
        MB_READ_KEYS            <= '0';
        MB_WAITn                <= '1';
        MB_ADDR                 <= (others => '0');
        KEY_DATA                <= (others => '0');
    end generate;


    -- An approximate millisecond generator.
    --
    process(Z80_RESETn, CTLCLKi)
    begin
        if Z80_RESETn = '0' then
            DELAY_TICKS             <= (others => '1');
            DELAY_US                <= (others => '0');
            DELAY_MS_CLK            <= '0';

        elsif rising_edge(CTLCLKi) then

            -- An approximate uS timer, the CTLCLK is taken to be 3.58MHz in MZ-700 mode or 2MHz in MZ-80A mode.
            if DELAY_TICKS = 0 then
                DELAY_US            <= DELAY_US + 1;
                if MODE_CPLD_MZ700 = '1' then
                    DELAY_TICKS     <= to_unsigned(4,  DELAY_TICKS'length);
                elsif MODE_CPLD_MZ80A = '1' then
                    DELAY_TICKS     <= to_unsigned(2,  DELAY_TICKS'length);
                else
                    DELAY_TICKS     <= to_unsigned(15, DELAY_TICKS'length);
                end if;
            else
                DELAY_TICKS         <= DELAY_TICKS - 1;
            end if;
            if DELAY_US >= to_unsigned(500, DELAY_US'length) then
                DELAY_MS_CLK        <= not DELAY_MS_CLK;
                DELAY_US            <= (others => '0');
            end if;
        end if;
    end process;

    -- D type Flip Flops used for the CPU frequency switching circuit. The changeover of frequencies occurs on the high level, the output clock remaining
    -- high until the falling edge of the clock being switched into.
    FFCLK1: process( SYSCLK, Z80_RESETn ) begin
        if Z80_RESETn = '0' then
            SYSCLK_Q           <= '0';

        -- If the system clock goes active high, process the inputs and set the D-type output.
        elsif( rising_edge(SYSCLK) ) then
            if ((DISABLE_BUSn = '1' or MB_BUSRQn = '0' or SCK_CTLSELn = '1') and CTLCLK_Q = '1') then
                SYSCLK_Q       <= '0';
            else
                SYSCLK_Q       <= '1';
            end if;
        end if;
    end process;
    FFCLK2: process( CTLCLKi, Z80_RESETn ) begin
        if Z80_RESETn = '0' then
            CTLCLK_Q           <= '1';

        -- If the control clock goes active high, process the inputs and set the D-type output.
        elsif( rising_edge(CTLCLKi) ) then
            if ((DISABLE_BUSn = '0' and SCK_CTLSELn = '0') and SYSCLK_Q = '1') then
                CTLCLK_Q       <= '0';
            else
                CTLCLK_Q       <= '1';
            end if;
        end if;
    end process;

    -- Mainboard Clock Select S-R latch 3.
    MBCLKSEL: process(Z80_CLKi, CS_SCK_SYSCLKn, CS_SCK_CTLCLKn, Z80_RESETn)
    begin
        if Z80_RESETn = '0' then
            SCK_CTLSELn        <= '1';
        elsif (Z80_CLKi='1' and Z80_CLKi'event) then
            if CS_SCK_SYSCLKn = '0'    or (MODE_CPLD_SWITCH = '1' and MODE_CPLD_MZ80A = '1') then
                SCK_CTLSELn    <= '1';
            elsif CS_SCK_CTLCLKn = '0' or (MODE_CPLD_SWITCH = '1' and MODE_CPLD_MZ700 = '1') then
                SCK_CTLSELn    <= '0';
            else
                null;
            end if;
        end if;
    end process;

    -- A Video Module signal serializer. Signals required by the Video Module but not accessible physically (without hardware hacks) are captured and serialised as a set of x 4 blocks, clocked by the video module,
    -- Reset synchronises the Video Module CPLD with the tranZPUter CPLD and the signals are sent during valid mainboard accesses.
    --
    MZ80ASERIALISER: if CPLD_HOST_HW = MODE_MZ80A generate
        SIGNALSERIALIZER: process(INCLK, Z80_RESETn)
            variable XMIT_CYCLE             : integer range 0 to 1;
        begin
            if Z80_RESETn = '0' then
                XMIT_CYCLE                  := 0;
                VIDEOMODULE_PRESENT         <= '0';

            elsif (INCLK='1' and INCLK'event) then

                -- Tight loop, sending current signal status on each clock. There are 16 signals to send and 4 data lines, so we need 4 cycles per data set.
                case XMIT_CYCLE is
                    when 0 =>
                        -- If we are accessing the mainboard then send across a valid signal set else mark it as invalid.
                        --
                        if SYSCLK_Q = '0' then
                            OUTDATA(3 downto 0) <= Z80_ADDR(14 downto 11);
                            OUTBUF              <= VZ80_IORQn & CS_VIDEO_WRn & CS_VIDEO_RDn & Z80_ADDR(15);
                        else
                            OUTDATA(3 downto 0) <= (others => '0');
                            OUTBUF              <= (others => '0');
                        end if;
                        XMIT_CYCLE              := 1;

                    when 1 =>
                        -- Double check, if we started with a valid mainboard cycle but the clock switched, or we started with an invalid mainboard
                        -- cycle and the clock switched to mainboard, then invalidate this cycle, otherwise send the final signals as captured at the 
                        -- start of the cycle.
                        if SYSCLK_Q = '0' and OUTBUF(3 downto 1) /= "000" then
                            OUTDATA(3 downto 0) <= OUTBUF(3 downto 0);
                        else
                            OUTDATA(3 downto 0) <= (others => '0');
                        end if;
                        VIDEOMODULE_PRESENT     <= '1';
                        XMIT_CYCLE              := 0;
                end case;
            end if;
        end process;

        -- Read from memory and IO devices within the FPGA.
        CS_VIDEO_RDn          <= '0'            when (CS_VIDEO_MEMn = '0' or CS_VIDEO_IOn = '0') and Z80_RDn = '0'
                                 else '1';

        -- Write to memory and IO devices within the FPGA. Duplicate the transaction to the FPGA for CPLD register writes 0x60:0x6F so that the FPGA can register current settings.
        CS_VIDEO_WRn          <= '0'            when (CS_VIDEO_MEMn = '0' or CS_VIDEO_IOn = '0' or CS_IO_EXXn = '0' or CS_IO_6XXn = '0') and Z80_WRn = '0'
                                 else '1';

        -- Pass through the addres and control signals to the FPGA.
        VZ80_IORQn            <= '0'            when Z80_IORQn = '0' and (Z80_RDn = '0' or Z80_WRn = '0')
                                 else '1';
    else generate
        VIDEOMODULE_PRESENT   <= '0';
        OUTDATA               <= (others => '0');
    end generate;

    -- Control Registers - This mirrors the Video Module control registers as we need to know when video memory is to be mapped into main memory.
    --
    -- IO Range for Graphics enhancements is set by the Video Mode registers at 0xF8->.
    --   0xF8=<val> sets the mode that of the Video Module. [2:0] - 000 (default) = MZ80A, 001 = MZ-700, 010 = MZ800, 011 = MZ80B, 100 = MZ80K, 101 = MZ80C, 110 = MZ1200, 111 = MZ2000.
    --   0xFD=<val> memory page register. [1:0] switches in 1 16Kb page (3 pages) of graphics ram to C000 - FFFF. Bits [1:0] = page, 00 = off, 01 = Red, 10 = Green, 11 = Blue.
    --
    CTRLREGISTERS: process( Z80_RESETn, Z80_CLKi, GRAM_PAGE_ENABLE, MZ80B_VRAM_HI_ADDR, MZ80B_VRAM_LO_ADDR )
    begin
        -- Ensure default values at reset.
        if Z80_RESETn = '0' then
            if CPLD_HOST_HW = MODE_MZ80A then
                MODE_VIDEO_MZ80A  <= '1';
            else
                MODE_VIDEO_MZ80A  <= '0';
            end if;
            MODE_VIDEO_MZ700      <= '0';
            if CPLD_HOST_HW = MODE_MZ800 then
                MODE_VIDEO_MZ800  <= '1';
            else 
                MODE_VIDEO_MZ800  <= '0';
            end if;
            MODE_VIDEO_MZ80B      <= '0';
            MODE_VIDEO_MZ80K      <= '0';
            MODE_VIDEO_MZ80C      <= '0';
            MODE_VIDEO_MZ1200     <= '0';
            MODE_VIDEO_MZ2000     <= '0';
            GRAM_PAGE_ENABLE      <= '0';
            MZ80B_VRAM_HI_ADDR    <= '0';
            MZ80B_VRAM_LO_ADDR    <= '0';
    
        elsif rising_edge(Z80_CLKi) then

            -- Setup the machine mode.
            if CS_FB_VMn = '0' and Z80_WRn = '0' then
                MODE_VIDEO_MZ80K  <= '0';
                MODE_VIDEO_MZ80C  <= '0';
                MODE_VIDEO_MZ1200 <= '0';
                MODE_VIDEO_MZ80A  <= '0';
                MODE_VIDEO_MZ700  <= '0';
                MODE_VIDEO_MZ800  <= '0';
                MODE_VIDEO_MZ80B  <= '0';
                MODE_VIDEO_MZ2000 <= '0';

                -- Bits [2:0] define the machine compatibility.
                --
                case to_integer(unsigned(Z80_DATA(2 downto 0))) is
                    when MODE_MZ80K =>
                        MODE_VIDEO_MZ80K  <= '1';
                    when MODE_MZ80C =>
                        MODE_VIDEO_MZ80C  <= '1';
                    when MODE_MZ1200 =>
                        MODE_VIDEO_MZ1200 <= '1';
                    when MODE_MZ80A =>
                        MODE_VIDEO_MZ80A  <= '1';
                    when MODE_MZ700 =>
                        MODE_VIDEO_MZ700  <= '1';
                    when MODE_MZ800 =>
                        MODE_VIDEO_MZ800  <= '1';
                    when MODE_MZ80B =>
                        MODE_VIDEO_MZ80B  <= '1';
                    when MODE_MZ2000 =>
                        MODE_VIDEO_MZ2000 <= '1';
                    when others =>
                end case;
            end if;

            -- memory page register. [1:0] switches in 16Kb page (1 of 3 pages) of graphics ram to C000 - FFFF. Bits [0] = page, 0 = Off, 1 = Enabled. This overrides all MZ700/MZ80B page switching functions. [7] 0 - normal, 1 - switches in CGROM for upload at D000:DFFF.
            if CS_FB_PAGEn = '0' and Z80_WRn = '0' then
                GRAM_PAGE_ENABLE          <= Z80_DATA(0);
            end if;

            -- MZ80B Z80 PIO.
            if CS_80B_PIOn = '0' and MODE_VIDEO_MZ80B = '1' and Z80_WRn = '0' then

                -- Write to PIO A.
                -- 7 = Assigns addresses $DOOO-$FFFF to V-RAM.
                -- 6 = Assigns addresses $5000-$7FFF to V-RAM.
                -- 5 = Changes screen to 80-character mode (L: 40-character mode).
                if Z80_ADDR(1 downto 0) = "00" then
                    MZ80B_VRAM_HI_ADDR    <= Z80_DATA(7);
                    MZ80B_VRAM_LO_ADDR    <= Z80_DATA(6);
                end if;
            end if;
        end if;
    end process;


    -- Memory decoding, taken directly from the definitions coded into the flashcfg tool in v1.1. The CPLD adds greater flexibility and mapping down to the byte level where needed.
    --
    -- Memory Modes:     0 - Default, normal Sharp MZ80A operating mode, all memory and IO (except tranZPUter control IO block) are on the mainboard
    --                   1 - As 0 except User ROM is mapped to tranZPUter RAM.
    --                   2 - TZFS, Monitor ROM 0000-0FFF, Main DRAM 0x1000-0xD000, User/Floppy ROM E800-FFFF are in tranZPUter memory. Two small holes of 2 bytes at F3FE and F7FE exist
    --                       for the Floppy disk controller, the fdc uses the rom as a wait detection by toggling the ROM lines according to WAIT, the Z80 at 2MHz hasnt enough ooomph to read WAIT and action it. 
    --                       NB: Main DRAM will not be refreshed so cannot be used to store data in this mode.
    --                   3 - TZFS, Monitor ROM 0000-0FFF, Main RAM area 0x1000-0xD000, User ROM 0xE800-EFFF are in tranZPUter memory block 0, Floppy ROM F000-FFFF are in tranZPUter memory block 1.
    --                       NB: Main DRAM will not be refreshed so cannot be used to store data in this mode.
    --                   4 - TZFS, Monitor ROM 0000-0FFF, Main RAM area 0x1000-0xD000, User ROM 0xE800-EFFF are in tranZPUter memory block 0, Floppy ROM F000-FFFF are in tranZPUter memory block 2.
    --                       NB: Main DRAM will not be refreshed so cannot be used to store data in this mode.
    --                   5 - TZFS, Monitor ROM 0000-0FFF, Main RAM area 0x1000-0xD000, User ROM 0xE800-EFFF are in tranZPUter memory block 0, Floppy ROM F000-FFFF are in tranZPUter memory block 3.
    --                       NB: Main DRAM will not be refreshed so cannot be used to store data in this mode.
    --                   6 - CPM, all memory on the tranZPUter board, 64K block 4 selected.
    --                       Special case for F3FE:F3FF & F7FE:F7FF (floppy disk paging vectors) which resides on the mainboard.
    --                   7 - CPM, F000-FFFF are on the tranZPUter board in block 4, 0040-CFFF and E800-EFFF are in block 5 selected, mainboard for D000-DFFF (video), E000-E800 (Memory control) selected.
    --                       Special case for 0000:00FF (interrupt vectors) which resides in block 4 and CPM vectors and two small holes of 2 bytes at F3FE and F7FE exist for the Floppy disk controller, the fdc
    --                       uses the rom as a wait detection by toggling the ROM lines according to WAIT, the Z80 at 2MHz hasnt enough ooomph to read WAIT and action it. 
    --                   8 - Monitor ROM (0000:0FFF) on mainboard, Main RAM (1000:CFFF) in tranZPUter bank 0 and video, memory mapped I/O, User/Floppy ROM on mainboard.
    --                       NB: Main DRAM will not be refreshed so cannot be used to store data in this mode.
    --                   9 - Monitor ROM 0000-0FFF and Main DRAM 0x1000-0xD000, video and memory mapped I/O are on the host machine, User/Floppy ROM E800-FFFF are in tranZPUter memory. 
    --                  10 - MZ700 Mode - 0000:0FFF is on the tranZPUter board in block 6, 1000:CFFF is on the tranZPUter board in block 0, D000:FFFF is on the mainboard.
    --                  11 - MZ700 Mode - 0000:0FFF is on the tranZPUter board in block 0, 1000:CFFF is on the tranZPUter board in block 0, D000:FFFF is on the tranZPUter in block 6.
    --                  12 - MZ700 Mode - 0000:0FFF is on the tranZPUter board in block 6, 1000:CFFF is on the tranZPUter board in block 0, D000:FFFF is on the tranZPUter in block 6.
    --                  13 - MZ700 Mode - 0000:0FFF is on the tranZPUter board in block 0, 1000:CFFF is on the tranZPUter board in block 0, D000:FFFF is inaccessible.
    --                  14 - MZ700 Mode - 0000:0FFF is on the tranZPUter board in block 6, 1000:CFFF is on the tranZPUter board in block 0, D000:FFFF is inaccessible.
    --                  15 - MZ800 Mode - Running on MZ800 hardware, configuration set according to MZ700/MZ800 mode.
    --                  21 - Access the FPGA memory by passing through the full 24bit Z80 address, typically from the K64F.
    --                  22 - Access to the host mainboard 64K address space only.
    --                  23 - Access all memory and IO on the tranZPUter board with the K64F addressing the full 512K RAM.
    --                  24 - All memory and IO are on the tranZPUter board, 64K block 0 selected.
    --                  25 - All memory and IO are on the tranZPUter board, 64K block 1 selected.
    --                  26 - All memory and IO are on the tranZPUter board, 64K block 2 selected.
    --                  27 - All memory and IO are on the tranZPUter board, 64K block 3 selected.
    --                  28 - All memory and IO are on the tranZPUter board, 64K block 4 selected.
    --                  29 - All memory and IO are on the tranZPUter board, 64K block 5 selected.
    --                  30 - All memory and IO are on the tranZPUter board, 64K block 6 selected.
    --                  31 - All memory and IO are on the tranZPUter board, 64K block 7 selected.
    --
    MEMORYMGMT: process(Z80_ADDR, Z80_WRn, Z80_RDn, Z80_IORQn, Z80_MREQn, Z80_M1n, MEM_MODE_LATCH, SYS_BUSACKni, CS_VIDEOn, CS_VIDEO_IOn, CS_IO_DXXn, CS_IO_EXXn, CS_IO_FXXn, CS_CPLD_CFGn, CS_CPLD_INFOn, MODE_CPLD_MB_VIDEOn, MAP_TZFS_BANK,
                        MAP_INHIBIT, MODE_CPLD_MZ700, MODE_CPLD_MZ800, MAP_0000_0FFF_ROM, MAP_E000_EFFF_ROM, MAP_F000_FFFF_ROM, MAP_1000_1FFF_CGROM, MAP_0000_0FFF_DRAM, MAP_1000_1FFF_DRAM, MAP_2000_2FFF_DRAM, MAP_3000_3FFF_DRAM, MAP_4000_4FFF_DRAM, 
                        MAP_5000_5FFF_DRAM, MAP_6000_6FFF_DRAM, MAP_7000_7FFF_DRAM, MAP_8000_8FFF_DRAM, MAP_9000_9FFF_DRAM, MAP_A000_AFFF_DRAM, MAP_B000_BFFF_DRAM, MAP_C000_CFFF_DRAM, MAP_D000_DFFF_DRAM, MAP_E000_EFFF_DRAM, MAP_F000_FFFF_DRAM, 
                        MAP_8000_8FFF_VRAM, MAP_9000_9FFF_VRAM, MAP_A000_AFFF_VRAM, MAP_B000_BFFF_VRAM, MAP_C000_CFFF_VRAM, MAP_D000_DFFF_VRAM, MAP_E000_E00F_IO, MODE_320x200, MODE_640x200)
    begin

        -- Memory action according to the configured memory mode. Not synchronous as we need to detect and act on address or signals long before a rising edge.
        --
        case to_integer(unsigned(MEM_MODE_LATCH(4 downto 0))) is

            -- Set 0 - default, no tranZPUter RAM access so hold the DISABLE_BUS signal inactive to ensure the CPU has continuous access to the
            -- mainboard resources, especially for Refresh of DRAM.
            when TZMM_ORIG => 
                Z80_HI_ADDRi        <= "00000000"; 
                Z80_RA_ADDRi        <= Z80_ADDR(15 downto 12);
                RAM_CSni            <= '1';
                RAM_WEni            <= '1';
                RAM_OEni            <= '1';
                CS_VIDEO_MEMn       <= '1';
                if  CS_VIDEOn = '0' then
                    CS_VIDEO_MEMn   <= Z80_MREQn;
                    DISABLE_BUSn    <= '1';
                else
                    DISABLE_BUSn    <= '1';
                end if;

            -- Whenever running in RAM ensure the mainboard is disabled to prevent decoder propagation delay glitches.
            when TZMM_BOOT => 
                Z80_HI_ADDRi        <= "00000000"; 
                Z80_RA_ADDRi        <= Z80_ADDR(15 downto 12);
                RAM_CSni            <= '0';
                CS_VIDEO_MEMn       <= '1';
                if CS_VIDEOn = '0' then
                    DISABLE_BUSn    <= '1';
                    RAM_WEni        <= '1';
                    RAM_OEni        <= '1';
                    CS_VIDEO_MEMn   <= Z80_MREQn;

                elsif( unsigned(Z80_ADDR(15 downto 0)) >= X"E800" and unsigned(Z80_ADDR(15 downto 0)) < X"F000") then
                    DISABLE_BUSn    <= '0';
                    RAM_OEni        <= Z80_RDn;
                    if unsigned(Z80_ADDR(15 downto 0)) >= X"EC00" then
                        RAM_WEni    <= Z80_WRn;
                    else
                        RAM_WEni    <= '1';
                    end if;

                else
                    DISABLE_BUSn    <= '1';
                    RAM_WEni        <= '1';
                    RAM_OEni        <= '1';
                end if;

            -- Set 2 - Monitor ROM 0000-0FFF, Main DRAM 0x1000-0xD000, User/Floppy ROM E800-FFFF are in tranZPUter memory. Two small holes of 2 bytes at F3FE and F7FE exist for the Floppy disk controller, the fdc uses the rom as a wait
            -- detection by toggling the ROM lines according to WAIT, the Z80 at 2MHz hasnt enough ooomph to read WAIT and action it. 
            -- NB: Main DRAM will not be refreshed so cannot be used to store data in this mode.
            when TZMM_TZFS => 

                -- FPGA Video
                if CS_VIDEOn = '0' then
                    CS_VIDEO_MEMn   <= Z80_MREQn;
                    DISABLE_BUSn    <= '1';
                    RAM_CSni        <= '1';
                    RAM_WEni        <= '1';
                    RAM_OEni        <= '1';

                -- Monitor/TZFS page locations 0000:0FFF, E800:FFFF
                elsif( (unsigned(Z80_ADDR(15 downto 0)) >= X"0000" and unsigned(Z80_ADDR(15 downto 0)) <= X"0FFF") or (unsigned(Z80_ADDR(15 downto 0)) >= X"E800" and unsigned(Z80_ADDR(15 downto 0)) <= X"FFFF" and not std_match(Z80_ADDR(15 downto 1), "11110-111111111")) ) then 
                    Z80_HI_ADDRi    <= "00000000"; 
                    Z80_RA_ADDRi    <= Z80_ADDR(15 downto 12);
                    DISABLE_BUSn    <= '0';
                    CS_VIDEO_MEMn   <= '1';
                    RAM_CSni        <= '0';
                    RAM_OEni        <= Z80_RDn;
                    if unsigned(Z80_ADDR(15 downto 0)) = X"E800" then
                        RAM_WEni    <= '1';
                    else
                        RAM_WEni    <= Z80_WRn;
                    end if;

                -- DRAM
                elsif(unsigned(Z80_ADDR(15 downto 0)) >= X"1000" and unsigned(Z80_ADDR(15 downto 0)) < X"D000") then
                    if CPLD_HOST_HW = MODE_MZ800 then
                        Z80_HI_ADDRi<= "00000110"; 
                    else
                        Z80_HI_ADDRi<= "00000000"; 
                    end if;
                    Z80_RA_ADDRi    <= Z80_ADDR(15 downto 12);
                    DISABLE_BUSn    <= '0';
                    CS_VIDEO_MEMn   <= '1';
                    RAM_CSni        <= '0';
                    RAM_OEni        <= Z80_RDn;
                    RAM_WEni        <= Z80_WRn;

                else
                    -- No action, defaults set to work directly on mainboard.
                    DISABLE_BUSn    <= '1';
                    CS_VIDEO_MEMn   <= '1';
                    RAM_CSni        <= '1';
                    RAM_WEni        <= '1';
                    RAM_OEni        <= '1';
                end if;

            -- Set 3 - Monitor ROM 0000-0FFF, Main RAM area 0x1000-0xD000, User ROM 0xE800-EFFF are in tranZPUter memory block 0, Floppy ROM F000-FFFF are in tranZPUter memory block 1.
            -- NB: Main DRAM will not be refreshed so cannot be used to store data in this mode.
            when TZMM_TZFS2 => 

                if CS_VIDEOn = '0' then
                    CS_VIDEO_MEMn   <= Z80_MREQn;
                    DISABLE_BUSn    <= '1';
                    RAM_CSni        <= '1';
                    RAM_WEni        <= '1';
                    RAM_OEni        <= '1';

                -- Monitor/TZFS page locations 0000:0FFF, E800:FFFF
                elsif( (unsigned(Z80_ADDR(15 downto 0)) >= X"0000" and unsigned(Z80_ADDR(15 downto 0)) <= X"0FFF") or (unsigned(Z80_ADDR(15 downto 0)) >= X"E800" and unsigned(Z80_ADDR(15 downto 0)) <= X"FFFF" and not std_match(Z80_ADDR(15 downto 1), "11110-111111111")) ) then 
                    if( (unsigned(Z80_ADDR(15 downto 0)) >= X"0000" and unsigned(Z80_ADDR(15 downto 0)) <= X"0FFF") or (unsigned(Z80_ADDR(15 downto 0)) >= X"E800" and unsigned(Z80_ADDR(15 downto 0)) <= X"EFFF" )) then
                        Z80_HI_ADDRi    <= "00000000"; 
                    else
                        -- Page in Bank 1 memory in F000:FFFF slot.
                        Z80_HI_ADDRi    <= "00000001"; 
                    end if;
                    Z80_RA_ADDRi    <= Z80_ADDR(15 downto 12);
                    DISABLE_BUSn    <= '0';
                    CS_VIDEO_MEMn   <= '1';
                    RAM_CSni        <= '0';
                    RAM_OEni        <= Z80_RDn;
                    if unsigned(Z80_ADDR(15 downto 0)) = X"E800" then
                        RAM_WEni    <= '1';
                    else
                        RAM_WEni    <= Z80_WRn;
                    end if;

                -- DRAM
                elsif(unsigned(Z80_ADDR(15 downto 0)) >= X"1000" and unsigned(Z80_ADDR(15 downto 0)) < X"D000") then
                    if CPLD_HOST_HW = MODE_MZ800 then
                        Z80_HI_ADDRi<= "00000110"; 
                    else
                        Z80_HI_ADDRi<= "00000000"; 
                    end if;
                    Z80_RA_ADDRi    <= Z80_ADDR(15 downto 12);
                    DISABLE_BUSn    <= '0';
                    CS_VIDEO_MEMn   <= '1';
                    RAM_CSni        <= '0';
                    RAM_OEni        <= Z80_RDn;
                    RAM_WEni        <= Z80_WRn;

                else
                    -- No action, defaults set to work directly on mainboard.
                    DISABLE_BUSn    <= '1';
                    CS_VIDEO_MEMn   <= '1';
                    RAM_CSni        <= '1';
                    RAM_WEni        <= '1';
                    RAM_OEni        <= '1';
                end if;

            -- Set 4 - Monitor ROM 0000-0FFF, Main RAM area 0x1000-0xD000, User ROM 0xE800-EFFF are in tranZPUter memory block 0, Floppy ROM F000-FFFF are in tranZPUter memory block 2.
            -- NB: Main DRAM will not be refreshed so cannot be used to store data in this mode.
            when TZMM_TZFS3 => 

                if CS_VIDEOn = '0' then
                    CS_VIDEO_MEMn   <= Z80_MREQn;
                    DISABLE_BUSn    <= '1';
                    RAM_CSni        <= '1';
                    RAM_WEni        <= '1';
                    RAM_OEni        <= '1';

                -- Monitor/TZFS page locations 0000:0FFF, E800:FFFF
                elsif( (unsigned(Z80_ADDR(15 downto 0)) >= X"0000" and unsigned(Z80_ADDR(15 downto 0)) <= X"0FFF") or (unsigned(Z80_ADDR(15 downto 0)) >= X"E800" and unsigned(Z80_ADDR(15 downto 0)) <= X"FFFF" and not std_match(Z80_ADDR(15 downto 1), "11110-111111111")) ) then 
                    if( (unsigned(Z80_ADDR(15 downto 0)) >= X"0000" and unsigned(Z80_ADDR(15 downto 0)) <= X"0FFF") or (unsigned(Z80_ADDR(15 downto 0)) >= X"E800" and unsigned(Z80_ADDR(15 downto 0)) <= X"EFFF" )) then
                        Z80_HI_ADDRi    <= "00000000"; 
                    else
                        -- Page in Bank 2 memory in F000:FFFF slot.
                        Z80_HI_ADDRi    <= "00000010"; 
                    end if;
                    Z80_RA_ADDRi    <= Z80_ADDR(15 downto 12);
                    DISABLE_BUSn    <= '0';
                    CS_VIDEO_MEMn   <= '1';
                    RAM_CSni        <= '0';
                    RAM_OEni        <= Z80_RDn;
                    if unsigned(Z80_ADDR(15 downto 0)) = X"E800" then
                        RAM_WEni    <= '1';
                    else
                        RAM_WEni    <= Z80_WRn;
                    end if;

                -- DRAM
                elsif(unsigned(Z80_ADDR(15 downto 0)) >= X"1000" and unsigned(Z80_ADDR(15 downto 0)) < X"D000") then
                    if CPLD_HOST_HW = MODE_MZ800 then
                        Z80_HI_ADDRi<= "00000110"; 
                    else
                        Z80_HI_ADDRi<= "00000000"; 
                    end if;
                    Z80_RA_ADDRi    <= Z80_ADDR(15 downto 12);
                    DISABLE_BUSn    <= '0';
                    CS_VIDEO_MEMn   <= '1';
                    RAM_CSni        <= '0';
                    RAM_OEni        <= Z80_RDn;
                    RAM_WEni        <= Z80_WRn;

                else
                    -- No action, defaults set to work directly on mainboard.
                    DISABLE_BUSn    <= '1';
                    CS_VIDEO_MEMn   <= '1';
                    RAM_CSni        <= '1';
                    RAM_WEni        <= '1';
                    RAM_OEni        <= '1';
                end if;

            -- Set 5 - Monitor ROM 0000-0FFF, Main RAM area 0x1000-0xD000, User ROM 0xE800-EFFF are in tranZPUter memory block 0, Floppy ROM F000-FFFF are in tranZPUter memory block 3.
            -- NB: Main DRAM will not be refreshed so cannot be used to store data in this mode.
            when TZMM_TZFS4 => 

                if CS_VIDEOn = '0' then
                    CS_VIDEO_MEMn   <= Z80_MREQn;
                    DISABLE_BUSn    <= '1';
                    RAM_CSni        <= '1';
                    RAM_WEni        <= '1';
                    RAM_OEni        <= '1';

                -- Monitor/TZFS page locations 0000:0FFF, E800:FFFF
                elsif( (unsigned(Z80_ADDR(15 downto 0)) >= X"0000" and unsigned(Z80_ADDR(15 downto 0)) <= X"0FFF") or (unsigned(Z80_ADDR(15 downto 0)) >= X"E800" and unsigned(Z80_ADDR(15 downto 0)) <= X"FFFF" and not std_match(Z80_ADDR(15 downto 1), "11110-111111111")) ) then 
                    if( (unsigned(Z80_ADDR(15 downto 0)) >= X"0000" and unsigned(Z80_ADDR(15 downto 0)) <= X"0FFF") or (unsigned(Z80_ADDR(15 downto 0)) >= X"E800" and unsigned(Z80_ADDR(15 downto 0)) <= X"EFFF" )) then
                        Z80_HI_ADDRi    <= "00000000"; 
                    else
                        -- Page in Bank 2 memory in F000:FFFF slot.
                        Z80_HI_ADDRi    <= "00000011"; 
                    end if;
                    Z80_RA_ADDRi    <= Z80_ADDR(15 downto 12);
                    DISABLE_BUSn    <= '0';
                    CS_VIDEO_MEMn   <= '1';
                    RAM_CSni        <= '0';
                    RAM_OEni        <= Z80_RDn;
                    if unsigned(Z80_ADDR(15 downto 0)) = X"E800" then
                        RAM_WEni    <= '1';
                    else
                        RAM_WEni    <= Z80_WRn;
                    end if;

                -- DRAM
                elsif(unsigned(Z80_ADDR(15 downto 0)) >= X"1000" and unsigned(Z80_ADDR(15 downto 0)) < X"D000") then
                    if CPLD_HOST_HW = MODE_MZ800 then
                        Z80_HI_ADDRi<= "00000110"; 
                    else
                        Z80_HI_ADDRi<= "00000000"; 
                    end if;
                    Z80_RA_ADDRi    <= Z80_ADDR(15 downto 12);
                    DISABLE_BUSn    <= '0';
                    CS_VIDEO_MEMn   <= '1';
                    RAM_CSni        <= '0';
                    RAM_OEni        <= Z80_RDn;
                    RAM_WEni        <= Z80_WRn;

                else
                    -- No action, defaults set to work directly on mainboard.
                    DISABLE_BUSn    <= '1';
                    CS_VIDEO_MEMn   <= '1';
                    RAM_CSni        <= '1';
                    RAM_WEni        <= '1';
                    RAM_OEni        <= '1';
                end if;

            -- Set 6 - CPM, all memory on the tranZPUter board, 64K block 4 selected.
            -- Two small holes of 2 bytes at F3FE and F7FE exist for the Floppy disk controller, the fdc uses the rom as a wait detection by toggling the ROM lines according to WAIT, the Z80 at 2MHz hasnt enough ooomph to read WAIT and action it. 
            when TZMM_CPM => 
                RAM_CSni            <= '0';
                CS_VIDEO_MEMn       <= '1';

                if (unsigned(Z80_ADDR(15 downto 0)) >= X"0000" and unsigned(Z80_ADDR(15 downto 0)) <= X"FFFF" and not std_match(Z80_ADDR(15 downto 1), "11110-111111111")) then 
                    DISABLE_BUSn    <= '0';
                    Z80_HI_ADDRi    <= "00000100"; 
                    Z80_RA_ADDRi    <= Z80_ADDR(15 downto 12);
                    RAM_OEni        <= Z80_RDn;
                    RAM_WEni        <= Z80_WRn;

                else
                    DISABLE_BUSn    <= '1';
                    Z80_HI_ADDRi    <= "00000000"; 
                    Z80_RA_ADDRi    <= Z80_ADDR(15 downto 12);
                    RAM_WEni        <= '1';
                    RAM_OEni        <= '1';
                end if;

            -- Set 7 - CPM, F000-FFFF are on the tranZPUter board in block 4, 0040-CFFF and E800-EFFF are in block 5 selected, mainboard for D000-DFFF (video), E000-E800 (Memory control) selected.
            -- Special case for 0000:00FF (interrupt vectors) which resides in block 4 and CPM vectors and two small holes of 2 bytes at F3FE and F7FE exist for the Floppy disk controller, the fdc
            -- uses the rom as a wait detection by toggling the ROM lines according to WAIT, the Z80 at 2MHz hasnt enough ooomph to read WAIT and action it. 
            when TZMM_CPM2 => 
                RAM_CSni            <= '0';
                CS_VIDEO_MEMn       <= '1';

                if CS_VIDEOn = '0' then
                    DISABLE_BUSn    <= '1';
                    Z80_HI_ADDRi    <= "00000000"; 
                    Z80_RA_ADDRi    <= Z80_ADDR(15 downto 12);
                    RAM_WEni        <= '1';
                    RAM_OEni        <= '1';
                    CS_VIDEO_MEMn   <= Z80_MREQn;

                elsif ((unsigned(Z80_ADDR(15 downto 0)) >= X"0000" and unsigned(Z80_ADDR(15 downto 0)) < X"0100") or (unsigned(Z80_ADDR(15 downto 0)) >= X"F000" and unsigned(Z80_ADDR(15 downto 0)) <= X"FFFF" and not std_match(Z80_ADDR(15 downto 1), "11110-111111111"))) then
                    DISABLE_BUSn    <= '0';
                    Z80_HI_ADDRi    <= "00000100"; 
                    Z80_RA_ADDRi    <= Z80_ADDR(15 downto 12);
                    RAM_OEni        <= Z80_RDn;
                    RAM_WEni        <= Z80_WRn;

                elsif(((unsigned(Z80_ADDR(15 downto 0)) >= X"0100" and unsigned(Z80_ADDR(15 downto 0)) < X"D000") or (unsigned(Z80_ADDR(15 downto 0)) >= X"E800" and unsigned(Z80_ADDR(15 downto 0)) < X"F000"))) then
                    DISABLE_BUSn    <= '0';
                    Z80_HI_ADDRi    <= "00000101"; 
                    Z80_RA_ADDRi    <= Z80_ADDR(15 downto 12);
                    RAM_OEni        <= Z80_RDn;
                    RAM_WEni        <= Z80_WRn;

                else
                    DISABLE_BUSn    <= '1';
                    Z80_HI_ADDRi    <= "00000000"; 
                    Z80_RA_ADDRi    <= Z80_ADDR(15 downto 12);
                    RAM_WEni        <= '1';
                    RAM_OEni        <= '1';
                end if;

            -- Set 8 - Monitor ROM 0000-0FFF on mainboard, Main DRAM 0x1000-0xD000 is in tranZPUter memory. 
            -- NB: Main DRAM will not be refreshed so cannot be used to store data in this mode.
            when TZMM_COMPAT => 
                RAM_CSni            <= '0';
                CS_VIDEO_MEMn       <= '1';
                Z80_HI_ADDRi        <= "00000000"; 
                Z80_RA_ADDRi        <= Z80_ADDR(15 downto 12);

                if CS_VIDEOn = '0' then
                    DISABLE_BUSn    <= '1';
                    RAM_WEni        <= '1';
                    RAM_OEni        <= '1';
                    CS_VIDEO_MEMn   <= Z80_MREQn;

                elsif((unsigned(Z80_ADDR(15 downto 0)) >= X"1000" and unsigned(Z80_ADDR(15 downto 0)) < X"D000")) then
                    DISABLE_BUSn    <= '0';
                    RAM_OEni        <= Z80_RDn;
                    RAM_WEni        <= Z80_WRn;

                else
                    DISABLE_BUSn    <= '1';
                    RAM_WEni        <= '1';
                    RAM_OEni        <= '1';
                end if;

            -- Set 9 - Monitor ROM 0000-0FFF and Main DRAM 0x1000-0xD000, video and memory mapped I/O are on the host machine, User/Floppy ROM E800-FFFF are in tranZPUter memory. 
            -- This mode is to allow a program running in tranZPUTer RAM Bank 0 - address E000:FFFF, to access host memory and I/O directly.
            when TZMM_HOSTACCESS =>
                if CS_VIDEOn = '0' then
                    CS_VIDEO_MEMn   <= Z80_MREQn;
                    DISABLE_BUSn    <= '1';
                    RAM_CSni        <= '1';
                    RAM_WEni        <= '1';
                    RAM_OEni        <= '1';

                -- 0000:E7FF are on the host.
                elsif( ((unsigned(Z80_ADDR(15 downto 0)) >= X"0000" and unsigned(Z80_ADDR(15 downto 0)) <= X"E7FF") and not std_match(Z80_ADDR(15 downto 1), "11110-111111111")) ) then 
                    Z80_HI_ADDRi    <= "00000000"; 
                    Z80_RA_ADDRi    <= Z80_ADDR(15 downto 12);
                    DISABLE_BUSn    <= '1';
                    CS_VIDEO_MEMn   <= '1';
                    RAM_CSni        <= '1';
                    RAM_OEni        <= '1';
                    RAM_WEni        <= '1';

                -- Upper tranZPUter RAM bank 0 address E800:FFFF execute on the tranZPUter.
                elsif(unsigned(Z80_ADDR(15 downto 0)) >= X"E800" and unsigned(Z80_ADDR(15 downto 0)) <= X"FFFF") then
                    Z80_HI_ADDRi    <= "00000000"; 
                    Z80_RA_ADDRi    <= Z80_ADDR(15 downto 12);
                    DISABLE_BUSn    <= '0';
                    CS_VIDEO_MEMn   <= '1';
                    RAM_CSni        <= '0';
                    RAM_OEni        <= Z80_RDn;
                    RAM_WEni        <= Z80_WRn;

                else
                    -- No action, defaults set to work directly on mainboard.
                    DISABLE_BUSn    <= '1';
                    CS_VIDEO_MEMn   <= '1';
                    RAM_CSni        <= '1';
                    RAM_WEni        <= '1';
                    RAM_OEni        <= '1';
                end if;

            -- Set 10 - MZ700 Mode - 0000:0FFF is on the tranZPUter board in block 6, 1000:CFFF is on the tranZPUter board in block 0, D000:FFFF is on the mainboard.
            when TZMM_MZ700_0 =>
                RAM_CSni            <= '0';
                CS_VIDEO_MEMn       <= '1';

                if CS_VIDEOn = '0' then
                    DISABLE_BUSn    <= '1';
                    Z80_HI_ADDRi    <= "00000000"; 
                    Z80_RA_ADDRi    <= Z80_ADDR(15 downto 12);
                    RAM_WEni        <= '1';
                    RAM_OEni        <= '1';
                    CS_VIDEO_MEMn   <= Z80_MREQn;

                elsif(((unsigned(Z80_ADDR(15 downto 0)) >= X"0000" and unsigned(Z80_ADDR(15 downto 0)) < X"1000"))) then
                    DISABLE_BUSn    <= '0';
                    Z80_HI_ADDRi    <= "00000110"; 
                    Z80_RA_ADDRi    <= Z80_ADDR(15 downto 12);
                    RAM_OEni        <= Z80_RDn;
                    RAM_WEni        <= Z80_WRn;

                elsif((unsigned(Z80_ADDR(15 downto 0)) >= X"1000" and unsigned(Z80_ADDR(15 downto 0)) < X"D000")) then
                    DISABLE_BUSn    <= '0';
                    Z80_HI_ADDRi    <= "00000000"; 
                    Z80_RA_ADDRi    <= Z80_ADDR(15 downto 12);
                    RAM_OEni        <= Z80_RDn;
                    RAM_WEni        <= Z80_WRn;

                else
                    DISABLE_BUSn    <= '1';
                    Z80_HI_ADDRi    <= "00000000"; 
                    Z80_RA_ADDRi    <= Z80_ADDR(15 downto 12);
                    RAM_WEni        <= '1';
                    RAM_OEni        <= '1';
                end if;

            -- Set 11 - MZ700 Mode - 0000:0FFF is on the tranZPUter board in block 0, 1000:CFFF is on the tranZPUter board in block 0, D000:FFFF is on the tranZPUter in block 6.
            when TZMM_MZ700_1 =>
                RAM_CSni            <= '0';
                CS_VIDEO_MEMn       <= '1';

                if(((unsigned(Z80_ADDR(15 downto 0)) >= X"0000" and unsigned(Z80_ADDR(15 downto 0)) < X"1000"))) then
                    DISABLE_BUSn    <= '0';
                    Z80_HI_ADDRi    <= "00000000"; 
                    Z80_RA_ADDRi    <= Z80_ADDR(15 downto 12);
                    RAM_OEni        <= Z80_RDn;
                    RAM_WEni        <= Z80_WRn;

                elsif((unsigned(Z80_ADDR(15 downto 0)) >= X"1000" and unsigned(Z80_ADDR(15 downto 0)) < X"D000")) then
                    DISABLE_BUSn    <= '0';
                    Z80_HI_ADDRi    <= "00000000"; 
                    Z80_RA_ADDRi    <= Z80_ADDR(15 downto 12);
                    RAM_OEni        <= Z80_RDn;
                    RAM_WEni        <= Z80_WRn;

                elsif(((unsigned(Z80_ADDR(15 downto 0)) >= X"D000" and unsigned(Z80_ADDR(15 downto 0)) <= X"FFFF"))) then
                    DISABLE_BUSn    <= '0';
                    Z80_HI_ADDRi    <= "00000110"; 
                    Z80_RA_ADDRi    <= Z80_ADDR(15 downto 12);
                    RAM_OEni        <= Z80_RDn;
                    RAM_WEni        <= Z80_WRn;

                else
                    DISABLE_BUSn    <= '1';
                    Z80_HI_ADDRi    <= "00000000"; 
                    Z80_RA_ADDRi    <= Z80_ADDR(15 downto 12);
                    RAM_WEni        <= '1';
                    RAM_OEni        <= '1';
                end if;

            -- Set 12 - MZ700 Mode - 0000:0FFF is on the tranZPUter board in block 6, 1000:CFFF is on the tranZPUter board in block 0, D000:FFFF is on the tranZPUter in block 6.
            when TZMM_MZ700_2 =>
                RAM_CSni            <= '0';
                CS_VIDEO_MEMn       <= '1';

                if(((unsigned(Z80_ADDR(15 downto 0)) >= X"0000" and unsigned(Z80_ADDR(15 downto 0)) < X"1000"))) then
                    DISABLE_BUSn    <= '0';
                    Z80_HI_ADDRi    <= "00000110"; 
                    Z80_RA_ADDRi    <= Z80_ADDR(15 downto 12);
                    RAM_OEni        <= Z80_RDn;
                    RAM_WEni        <= Z80_WRn;

                elsif((unsigned(Z80_ADDR(15 downto 0)) >= X"1000" and unsigned(Z80_ADDR(15 downto 0)) < X"D000")) then
                    DISABLE_BUSn    <= '0';
                    Z80_HI_ADDRi    <= "00000000"; 
                    Z80_RA_ADDRi    <= Z80_ADDR(15 downto 12);
                    RAM_OEni        <= Z80_RDn;
                    RAM_WEni        <= Z80_WRn;

                elsif(((unsigned(Z80_ADDR(15 downto 0)) >= X"D000" and unsigned(Z80_ADDR(15 downto 0)) <= X"FFFF"))) then
                    DISABLE_BUSn    <= '0';
                    Z80_HI_ADDRi    <= "00000110"; 
                    Z80_RA_ADDRi    <= Z80_ADDR(15 downto 12);
                    RAM_OEni        <= Z80_RDn;
                    RAM_WEni        <= Z80_WRn;

                else
                    DISABLE_BUSn    <= '1';
                    Z80_HI_ADDRi    <= "00000000"; 
                    Z80_RA_ADDRi    <= Z80_ADDR(15 downto 12);
                    RAM_WEni        <= '1';
                    RAM_OEni        <= '1';
                end if;

            -- Set 13 - MZ700 Mode - 0000:0FFF is on the tranZPUter board in block 0, 1000:CFFF is on the tranZPUter board in block 0, D000:FFFF is inaccessible.
            when TZMM_MZ700_3 =>
                RAM_CSni            <= '0';
                CS_VIDEO_MEMn       <= '1';

                if(((unsigned(Z80_ADDR(15 downto 0)) >= X"0000" and unsigned(Z80_ADDR(15 downto 0)) < X"1000"))) then
                    DISABLE_BUSn    <= '0';
                    Z80_HI_ADDRi    <= "00000000"; 
                    Z80_RA_ADDRi    <= Z80_ADDR(15 downto 12);
                    RAM_OEni        <= Z80_RDn;
                    RAM_WEni        <= Z80_WRn;

                elsif((unsigned(Z80_ADDR(15 downto 0)) >= X"1000" and unsigned(Z80_ADDR(15 downto 0)) < X"D000")) then
                    DISABLE_BUSn    <= '0';
                    Z80_HI_ADDRi    <= "00000000"; 
                    Z80_RA_ADDRi    <= Z80_ADDR(15 downto 12);
                    RAM_OEni        <= Z80_RDn;
                    RAM_WEni        <= Z80_WRn;

                elsif(((unsigned(Z80_ADDR(15 downto 0)) >= X"D000" and unsigned(Z80_ADDR(15 downto 0)) <= X"FFFF"))) then
                    DISABLE_BUSn    <= '1';
                    Z80_HI_ADDRi    <= "00000000"; 
                    Z80_RA_ADDRi    <= Z80_ADDR(15 downto 12);
                    RAM_WEni        <= '1';
                    RAM_OEni        <= '1';

                else
                    DISABLE_BUSn    <= '1';
                    Z80_HI_ADDRi    <= "00000000"; 
                    Z80_RA_ADDRi    <= Z80_ADDR(15 downto 12);
                    RAM_WEni        <= '1';
                    RAM_OEni        <= '1';
                end if;

            -- Set 14 - MZ700 Mode - 0000:0FFF is on the tranZPUter board in block 6, 1000:CFFF is on the tranZPUter board in block 0, D000:FFFF is inaccessible.
            when TZMM_MZ700_4 =>
                RAM_CSni            <= '0';
                CS_VIDEO_MEMn       <= '1';

                if(((unsigned(Z80_ADDR(15 downto 0)) >= X"0000" and unsigned(Z80_ADDR(15 downto 0)) < X"1000"))) then
                    DISABLE_BUSn    <= '0';
                    Z80_HI_ADDRi    <= "00000110"; 
                    Z80_RA_ADDRi    <= Z80_ADDR(15 downto 12);
                    RAM_OEni        <= Z80_RDn;
                    RAM_WEni        <= Z80_WRn;

                elsif((unsigned(Z80_ADDR(15 downto 0)) >= X"1000" and unsigned(Z80_ADDR(15 downto 0)) < X"D000")) then
                    DISABLE_BUSn    <= '0';
                    Z80_HI_ADDRi    <= "00000000"; 
                    Z80_RA_ADDRi    <= Z80_ADDR(15 downto 12);
                    RAM_OEni        <= Z80_RDn;
                    RAM_WEni        <= Z80_WRn;

                elsif(((unsigned(Z80_ADDR(15 downto 0)) >= X"D000" and unsigned(Z80_ADDR(15 downto 0)) <= X"FFFF"))) then
                    DISABLE_BUSn    <= '1';
                    Z80_HI_ADDRi    <= "00000000"; 
                    Z80_RA_ADDRi    <= Z80_ADDR(15 downto 12);
                    RAM_WEni        <= '1';
                    RAM_OEni        <= '1';

                else
                    DISABLE_BUSn    <= '1';
                    Z80_HI_ADDRi    <= "00000000"; 
                    Z80_RA_ADDRi    <= Z80_ADDR(15 downto 12);
                    RAM_WEni        <= '1';
                    RAM_OEni        <= '1';
                end if;
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
