pdsmart/tranZPUter/software/asm/SFD700.asm

; ROM of K&P SFD700 interface

; data areas

; 1000 1 Latest FDC command byte 
; 1001 1 Motor on flag, 01 = on, 00 = off 
; 1002 4 Track 0 flags for each drive ( 1 to 4 ) 
; 1006 1 Retry count 
; 1007 1 Not sure of this one? 
; 1008 1 Drive Number ( 0 to 3 ) 
; 1009 2 Logical Sector Number ( 0 to 1119 ) 
; 100B 1 Bytes to read (after all sectors are read)
; 100C 1 Number of sectors to read
; or
; 100B 2 Bytes to read
; 100D 2 Memory Load address 
; 100F 1 Current track No. ( 0 to 69 ) 
; 1010 1 Current Sector No. ( 1 to 16 ) 
; 1011 1 Start track No. ( 0 to 69 ) 
; 1012 1 Start Sector No. ( 1 to 16 )


; Controller register
; $D8	; Command Register (write)
; $D8	; Status Register (read)
; $D9	; Track Register (write)
: $DA	; Sector Register (write)
: $DB	; Data Register	(read/write)
; $DC	; Drive/Motor select (write)
; $DD	; Side/Head select (write)


f000 00        NOP     			;ID for interface detection
f001 110810    LD      DE,1008H		;nach
f004 21DDF0    LD      HL,0F0DDH	;von
f007 010B00    LD      BC,000BH		;11 bytes 00 00 00 00 01 00 CE 00 00 00 00
f00a EDB0      LDIR    			;BC=0, HL=F0E8, DE=1013
f00c CD51F1    CALL    0F151H		;init 1001-1005, port $DC mit $00
f00f CD0900    CALL    0009H		;NL
f012 11A1F0    LD      DE,0F0A1H	;msg BOOT DRIVE?
f015 CD1500    CALL    0015H		;prt
f018 11A311    LD      DE,11A3H		;kbd buffer
f01b CD0300    CALL    0003H		;get line
f01e 1A        LD      A,(DE)		;get 1st char
f01f FE1B      CP      1BH		;brk?
f021 CA8900    JP      Z,0098H		;yes
f024 210C00    LD      HL,000CH
f027 19        ADD     HL,DE		;skip around msg, 11A3+0C=11AF
f028 7E        LD      A,(HL)		;get char
f029 FE0D      CP      0DH		;CR?
f02b 280D      JR      Z,0F03AH		;yes, default drive 1
f02d CDF903    CALL    03F9H		;ASCII to hex (A)
f030 38DD      JR      C,0F00FH		;nohex, error, again
f032 3D        DEC     A		;-1
f033 FE04      CP      04H		;drive >4?
f035 30D8      JR      NC,0F00FH	;error, again
f037 320810    LD      (1008H),A	;save drive no -1 (0 to 3)
f03a DD210810  LD      IX,1008H		;drive no
f03e CDBAF1    CALL    0F1BAH		;read sector 1 of trk 0
f041 2100CE    LD      HL,0CE00H	;dsk buffer
f044 11CCF0    LD      DE,0F0CCH	;=02 mst dsk flag (changed to 03)
f047 0607      LD      B,07H		;check for #02,"IPLPRO"
f049 4E        LD      C,(HL)
f04a 1A        LD      A,(DE)
f04b B9        CP      C
f04c C28CF0    JP      NZ,0F08CH	;error no master dsk	
f04f 23        INC     HL		;nxt char
f050 13        INC     DE		;nxt char
f051 10F6      DJNZ    0F049H		;nxt char
f053 CD0900    CALL    0009H		;NL
f056 11BCF0    LD      DE,0F0BCH
f059 CD1500    CALL    0015H		;msg K&P IS LOADING
f05c 1107CE    LD      DE,0CE07H
f05f CD1500    CALL    0015H		;prt prog name
f062 2A16CE    LD      HL,(0CE16H)	;load address
f065 DD7505    LD      (IX+05H),L	;to 100D/100E
f068 DD7406    LD      (IX+06H),H
f06b 2A14CE    LD      HL,(0CE14H)	;size
f06e DD7503    LD      (IX+03H),L	;to 100B/100C
f071 DD7404    LD      (IX+04H),H
f074 2A1ECE    LD      HL,(0CE1EH)	;logical sector number
f077 DD7501    LD      (IX+01H),L	;to 1009/100A
f07a DD7402    LD      (IX+02H),H
f07d CDBAF1    CALL    0F1BAH
f080 CD51F1    CALL    0F151H
f083 2A18CE    LD      HL,(0CE18H)	;exec address
f086 E9        JP      (HL)

f087 11AEF0    LD      DE,0F0AEH	;msg LOADING ERROR
f08a 1803      JR      0F08FH

f08c 11E8F0    LD      DE,0F0E8H	;msg THIS DISKETTE IS NOT MASTER
f08f CD0900    CALL    0009H
f092 CD1500    CALL    0015H
f095 CD0900    CALL    0009H
f098 11D3F0    LD      DE,0F0D3H
f09b CD3000    CALL    0030H		;play melody
f09e C3A200    JP      00A2H		;warm start

f0a1	       db      "BOOT DRIVE ?",#0D

f0ae           db      "LOADING ERROR",#0D

f0bc           db      "K&P IS LOADING ",#0D

f0cc           db      #02 ; changed to 03
f0cd           db      "IPLPRO"

;melody data
f0d3	       db      "A0",#D7,"ARA",#D7,"AR",#0D
f0dd	       db      ,#00,#00,#00,#00,#01,#00,#CE,#00,#00,#00,#00
 
f0e8           db      "THIS DISKETTE IS NOT MASTER",#0D

f104 3A0110    LD      A,(1001H)	;motor on flag
f107 0F        RRCA    			;motor off?
f108 D438F1    CALL    NC,0F138H	;yes, set motor on and wait
f10b DD7E00    LD      A,(IX+00H)	;drive no
f10e F684      OR      84H		;
f110 D3DC      OUT     (0DCH),A		;Motor on for drive 0-3
f112 AF        XOR     A
f113 320010    LD      (1000H),A	;clr latest FDC command byte
f116 210000    LD      HL,0000H
f119 2B        DEC     HL
f11a 7C        LD      A,H
f11b B5        OR      L
f11c CA9DF2    JP      Z,0F29DH		;reset and msg THIS DISKETTE IS NOT MASTER
f11f DBD8      IN      A,(0D8H)		;state reg
f121 2F        CPL     
f122 07        RLCA    
f123 38F4      JR      C,0F119H		;wait on motor off (bit 7)
f125 DD4E00    LD      C,(IX+00H)	;drive no
f128 210210    LD      HL,1002H		;1 track 0 flag for each drive
f12b 0600      LD      B,00H
f12d 09        ADD     HL,BC		;compute related flag 1002/1003/1004/1005
f12e CB46      BIT     0,(HL)		;
f130 2005      JR      NZ,0F137H	;no
f132 CD64F1    CALL    0F164H		;
f135 CBC6      SET     0,(HL)		;set bit 0 of trk 0 flag
f137 C9        RET     

;motor on
f138 3E80      LD      A,80H
f13a D3DC      OUT     (0DCH),A		;Motor on
f13c 0610      LD      B,10H		
f13e CDC7F2    CALL    0F2C7H		;wait loop2
f141 10FB      DJNZ    0F13EH		;16 times
f143 3E01      LD      A,01H
f145 320110    LD      (1001H),A	;motor on flag on
f148 C9        RET     

;command 1b output
f149 3E1B      LD      A,1BH		;1x = SEEK
f14b CD71F1    CALL    0F171H		;command 1b output
f14e E699      AND     99H
f150 C9        RET     

;init/reset flags, set motor off
f151 AF        XOR     A
f152 D3DC      OUT     (0DCH),A		;Motor on/off
f154 320210    LD      (1002H),A	;track 0 flag drive 1
f157 320310    LD      (1003H),A	;track 0 flag drive 2
f15a 320410    LD      (1004H),A	;track 0 flag drive 3
f15d 320510    LD      (1005H),A	;track 0 flag drive 4
f160 320110    LD      (1001H),A	:motor on flag
f163 C9        RET
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
